Baphomet2015/Formant_V2/Doc/Formant_V2_Capitulo_05.docx

# 1 formant v2: módulos

En este capítulo se analizarán los distintos módulos que integran el Formant V2.

Para cada módulo se detallarán las modificaciones realizadas (en caso de haberlas) y se dará referencia del capítulo que recoge la información del módulo en cuestión en el documento original del formant (ElektorFormantMusicSynthesiser.pdf).

Las mejoras introducidas han dotado al Formant V2 de una mayor capacidad y versatilidad de utilización pero siempre manteniendo intacta la esencia del diseño original, esto es, la generación de un sonido puramente analógico que es la característica más importante de este sintetizador de música tan especial.

## 1.1 módulo interfaz de teclado

Documentación original ElektorFormantMusicSynthesiser.pdf: Capítulos 2 y 3

Con el fin de dotar al Formant V2 de una mayor capacidad de control y versatilidad, se ha optado por sustituir el teclado clásico original por una interfaz MIDI.

Las ventajas de esta modificación son evidentes,

- Posibilidad de utilización de un moderno teclado MIDI.
- Integración del Formant V2 en un sistema de generación de música por ordenador.

La siguiente figura ilustra el interfaz propuesto,

INTERFACE TECLADO ORIGINAL FORMANT

KOV

GATE

MIDI IN

MIDI THRU

CONTROLADOR

MIDI

KBV

GATE

C

E

B

D

Figura 1. Diagrama de la interfaz de teclado MIDI

Nota:

Los puntos B, C, D y E son las señales correspondientes en el esquema de la interfaz de teclado original del Formant.

Este hecho sin embargo plantea diversos problemas técnicos.

En el diseño original del Formant se utilizó un teclado SKA de 37 teclas (3 octavas) en el cual, cada tecla accionaba dos “pulsadores” independientes, uno era utilizado para la generación de una cierta tensión correspondiente a la tecla pulsada (señal KOV que posteriormente controlaba los VCOs y VCFs) y otro erautilizado en la generación del pulso que se utiliza para disparar los diversos módulos que intervienen en el modelado del sonido (VCAs, ADSRs).

El primer paso para poder utilizar una señal MIDI será la implementación de una interfaz “MIDI → 1V/Octava” que por un lado implemente la interfaz MIDI con el exterior y por otro permita obtener las dos señales que generaba el teclado clásico del formant, esto es, la señal KBV y la señal GATE y que posteriormente se introducirán en el circuito original e interfaz de teclado el cual a su vez proporcionará las señales KOV y GATE al resto de módulos.

Otra consideración en el diseño es que como se ha comentado, el teclado original del formant disponía de 3 octavas, pero en la actualidad es difícil encontrar teclados MIDI con tres octavas por lo que se ha optado por ampliar la capacidad total del teclado a 4 octavas.

### 1.1.1 señal kbv

El Formant es un sintetizador de tecnología “1V / Octava”, esto significa que para cada aumento de 1V en la entrada, la frecuencia de salida aumentará en una octava (es decir, en un factor de 2).

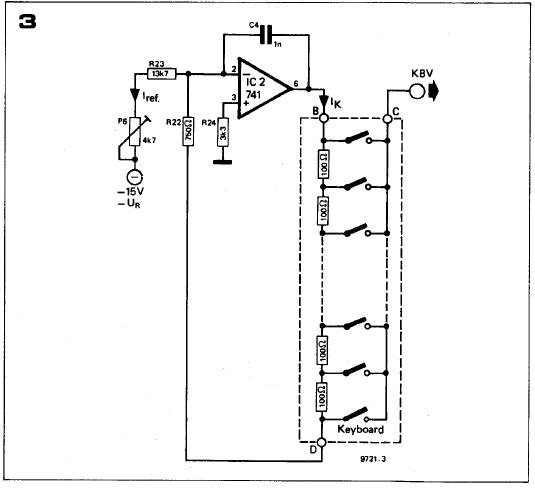
[picture p85: figure]

Cada octava tiene 12 semitonos por lo que obtenemos 1V/12 = 83,3mV por semitono, en el diseño original del Formant esta tensión se consigue mediante un divisor de tensión por el que circula una corriente constante (ver figura 3, en el capítulo 2 de la documentación original), de esta forma además se consigue que en caso de pulsar dos o más teclas simultáneamente bien accidentalmente o intencionadamente, solo se obtenga la nota de la tecla más grave, obteniendo así la característica de teclado monofónico del Formant, esta tensión es la que genera la señal KBV (Keyboard Voltage) como salida del generador 1V/Octava.

Figura 2. Generador 1V/Octava original.

Este circuito debe ser modificado de acuerdo al nuevo requerimiento de funcionamiento, el circuito resultante es el mostrado a continuación,

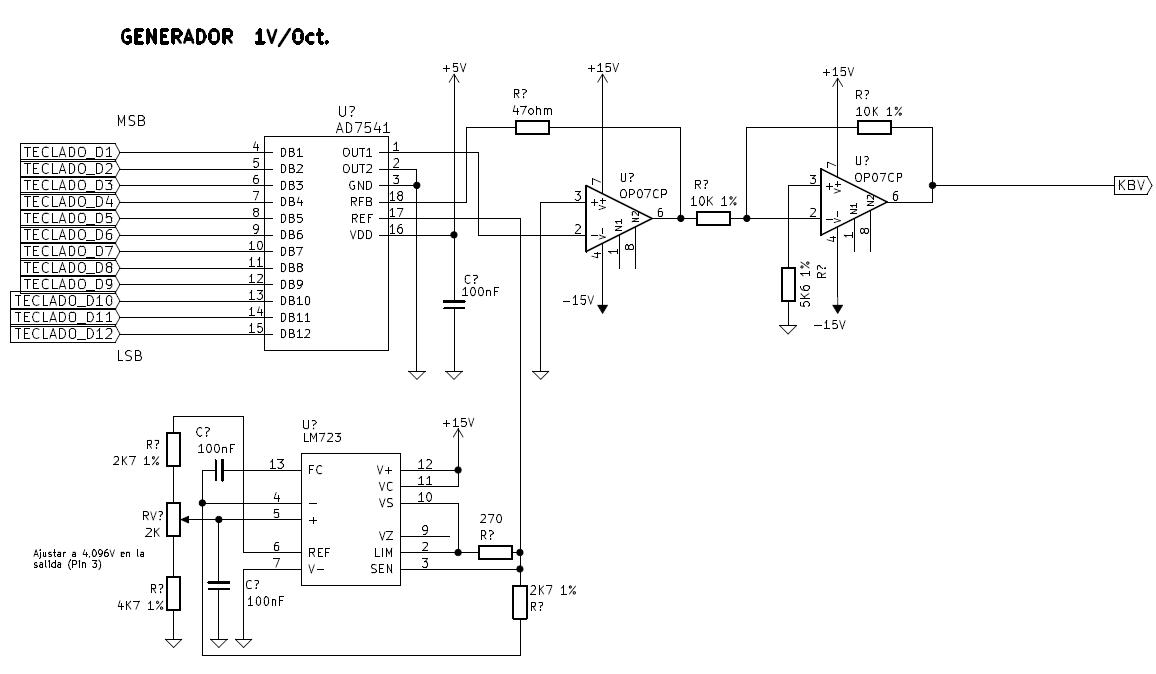
[picture p86: figure]

Figura 3. Generador 1V/Octava MIDI.

Como se puede apreciar, el circuito propuesto está implementado entorno a un conversor Digital/Analógico DAC de 12 Bits, el AD7541 de Analog Devices.

Este conversor recibe en sus entradas un cierto código y genera en su salida una tensión equivalente.

La tensión de referencia de este conversor se obtiene de un regulador muy preciso y estable implementado con un circuito LM723 (el mismo que se utiliza en la fuente de alimentación para obtener las tensiones generales de +15V, -15V y +5V). Este regulador estará ajustado para que su salida genere una tensión de 4,096 voltios, que utilizada como tensión de referencia para el DAC permitirá obtener tensiones en múltiplos de 1mV.

#### 1.1.1.1 Ajuste de la tensión de referencia

Se deberá ajustar la tensión de salida del LM723 medida en la entrada REF (pin 17) del AD7541, para obtener una tensión de 4,096V.

Dado que el conversor D/A posee 12Bits de resolución, esto permitirá obtener 4096 pasos, lo cual unido a la utilización de una tensión de referencia de 4,096V permite obtener tensiones de 1mV lo que finalmente conllevará en la obtención de las tensiones en incrementos de 83mV necesarios para implementar la característica 1V/Octava.

El hecho de utilizar un conversor D/A de 12Bits, unido a la tensión de referencia de 4,096V permite además abarcar el rango de 4 octavas propuesto.

El controlador MIDI cargará en el registro de salida formado por los dos C.I. 74HC593 el código equivalente a la tecla pulsada, este código es el que a su vez sirve de entrada para el código de entrada en el DAC.

### 1.1.2 señal gate

La segunda señal que se debe obtener del teclado es la denominada GATE, esto es un pulso de tensión que se genera cuando se pulsa alguna tecla en el teclado y que es utilizado como señal de disparo de diversos módulos del Formant (ADSR, VCAs, VCFs etc).

Esta señal que en el Formant original era generada por el segundo pulsador asociado a cada tecla y que se obtenía en los puntos A y E del teclado será generada directamente desde el circuito de interfaz MIDI e introducida finalmente en el punto E (GATE) del circuito de interfaz de teclado original.

### 1.1.3 señal kov

La señal KOV (Keyboard Output Voltage) es la señal más importante del Formant ya que comanda prácticamente todos los módulos del sintetizador.

Se genera a partir de la señal KBV, obtenida desde el circuito que realiza la interfaz MIDI y posterior característica 1V/Octava y es la resultante de “sumar” a esta señal KBV las tensiones aportadas por los potenciometros COARSE, FINE, PORTAMENTO y FM provinientes de la interfaz de teclado.

El circuito KOV propuesto se muestra en la siguiente figura,

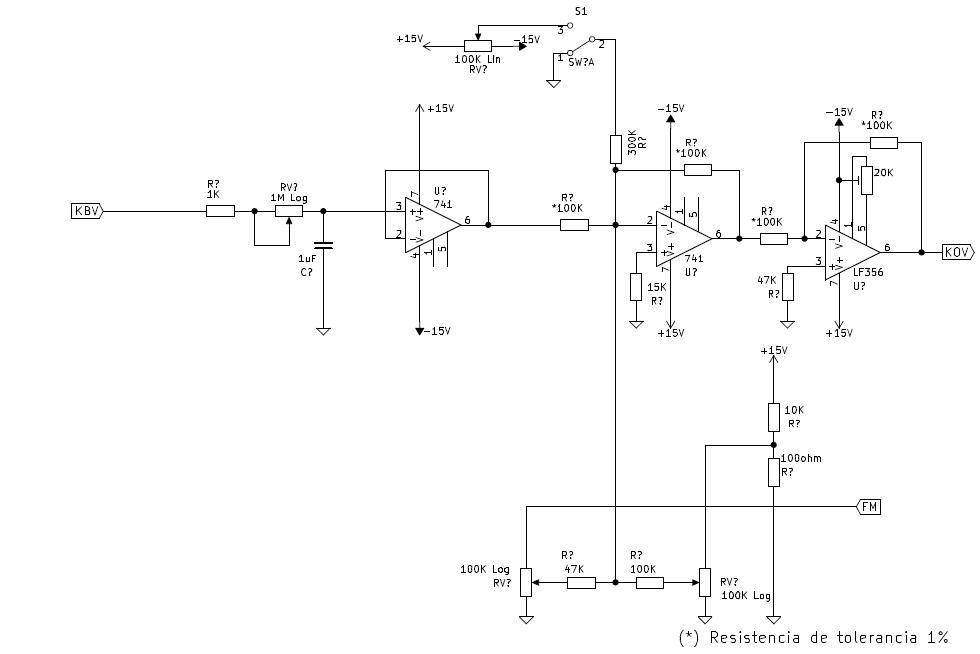
[picture p87: figure]

Figura 4. Circuito KOV.

La nueva versión difiere en gran medida de la original del Formant ya que, entre otras cosas elimina la etapa “Sample & Hold” del diseño original, efectivamente en el diseño original la señal KBV se inyectaba a una etapa de Sample & Hold con el fin de mantener la tensión de la tecla pulsada cuando el usuario deja de pulsar dicha tecla, esto es necesario para poder efectuar algunos efectos tales como el “portamento”. Debido al diseño original, cuando el usuario dejaba de pulsar una tecla la tensión generada por dicha tecla desaparecía inmediatamente lo que hacía imposible obtener el efecto de portamento, para ello se incluyó un circuito de Sample & Hold, el cual “muestreaba y retenía” la tensión de la tecla aún después de que dicha tensión desapareciera al dejar de pulsar la tecla, en el nuevo diseño esta etapa de retención es innecesaria ahora ya que el controlador MIDI cuando recibe el comando de tecla pulsada calcula el código correspondiente a dicha tecla y lo carga en el registro formado por los dos circuitos HC595 que alimentan la entrada del conversor D/A sustituyendo el código que previamente exista, posteriormente cuando el usuario deja de pulsar la tecla, el código de dicha tecla permanecerá en el registro dado que el controlador MIDI NO lo elimina, esto hace que la salida del D/A mantenga la tensión de dicha tecla aún después de que el usuario haya dejado de pulsar la tecla correspondiente, haciendo innecesaria la operación de retención o Sample & Hold.

La señal KBV se inyecta directamente al potenciometro de 1M que junto con el condensador de 1uF y el operacional en modo seguidor de tensión permiten obtener el efecto de portamento, tal y como se hacía en el diseño original.

Finalmente la señal KBV acondicionada se suma al circuito sumador de las tensiones de COARSE, FINE y FM, en esta parte el diseño original aportaba una compensación de offset para poder ajustar dicho offset final que en el nuevo diseño se elimina, sustituyendolo por el offset del amplificador operacional final.

#### 1.1.3.1 Ajuste del offset final.

Para ajustar el offset final se deberá inicializar el interfaz MIDI, esto se consigue al dar alimentación (power ON) o bien pulsando el pulsador de RESET general del Formant.

Después de inicializar el interfaz NO se debe pulsar ninguna tecla en el teclado, dado que inmediatamente después de la inicialización del interfaz, el código cargado en el D/A es 0 por lo que la señal KBV es 0 voltios.

Con un multímetro en la escala de voltios (o milivoltios si está disponible) se deberá ajustar el valor de la tensión KOV a 0 voltios, idealmente la tensión de la señal KOV deberá medirse en el circuito “receptor” de las señales GATE y KOV con el fin de incluir en la medida las posibles pérdidas de tensión que se pudieran producir en el cable que lleva la señal KOV hasta la etapa receptora de estas señales.

### 1.1.4 etapa receptora de las señales kov y gate

El diseño original del Formant incorpora una etapa receptora de las señales KOV y GATE, la cual recibe dichas señales desde el circuito generador y “compensa” las posibles pérdidas en dichas señales debidas por ejemplo a la longitud de los cables que las conectan.

Esta etapa permanece sin cambios respecto al diseño original, (ver figura 5, en el capítulo 3 de la documentación original).

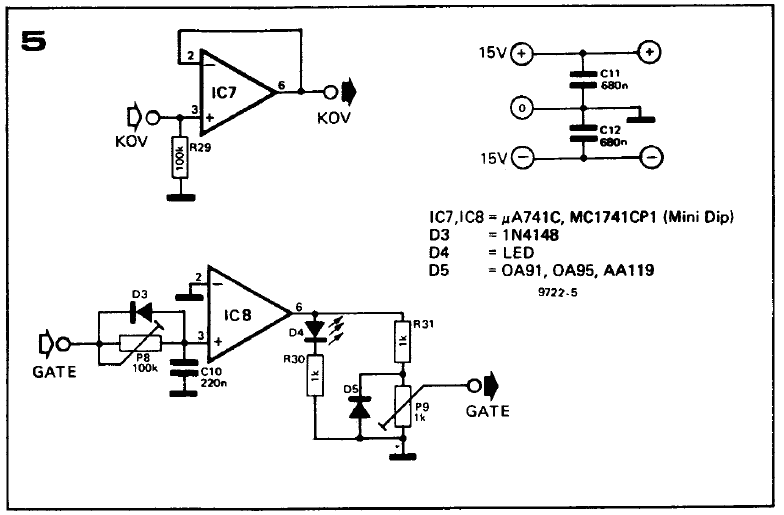
[picture p88: figure]

### 1.1.5 interfaz midi

La interfaz MIDI esta implementada utilizando un microcontrolador de tecnología openSource de Arduino, concretamente el modelo Arduino Nano.

Este microcontrolador recibe la señal MIDI-IN, decodifica los mensajes que se pueden utilizar para el control del Formant V2 y genera las señales correspondientes.

El canal MIDI que se asigna al Formant deberá ser fijado con los microinterruptores de configuración dispuestos a tal efecto.

Finalmente existe un pulsador de TEST para tareas de depuración y comprobación de funcionamiento, para activar el modo test se deberá seguir la siguiente operativa:

- Conectar el microcontrolador (utilizando el conector USB el mismo) con un ordenador (PC, portátil etc).

Atención:

Dependiendo de la versión de sistema operativo, es posible que sea necesario instalar determinados drivers, en este caso visitar el sitio web oficial de Arduino,

https://www.arduino.cc/en/Guide/Windows#

- Mantener pulsado el pulsador de TEST mientras se conecta el Formant V2 (power ON), al hacerlo y tras el arranque del microcontrolador, el Led de “señal MIDI” parpadeará indicando que se ha entrado en el modo test.
- Utilizar un programa de tipo Monitor Serie convencional para poder recibir la información enviada por el microcontrolador, seleccionando el puerto serie que ha montado el cable utilizado, normalmente estos puertos serie se reconocen porque si identifican con un valor COM distinto de COM1 o COM2 (puede ser COM3, COM4 o mayor).

Importante:

Se debe seleccionar una velocidad de transmisión en el programa monitor de 31250 Bps debido a que es la velocidad de operación del interfaz MIDI.

No todos los terminales serie permiten seleccionar esta velocidad por lo que dicho programa deberá tener la posibilidad de elegir esta velocidad.

Una vez establecida la comunicación entre el interfaz MIDI y el ordenador, se deberá recibir en el programa terminal un texto similar a este,

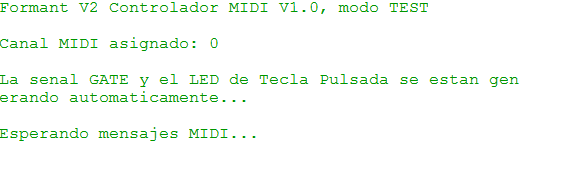
[picture p89: figure]

Ahora, si se reciben mensajes MIDI, estos NO se ejecutarán sino que la información relativa a los mismos será decodificada y enviada al programa terminal, como por ejemplo,

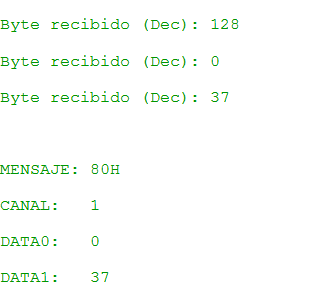
[picture p90: figure]

La interfaz MIDI del Formant V2 no solo permite controlar el teclado, respondiendo a los mensajes Note ON y Note OFF sino que también soporta las siguientes funciones:

- Control de volumen general del canal.

Mensaje MIDI Control Change (cambio de control), Control Change 7: Volumen

Este mensaje MIDI permite ajustar el volumen general de salida del Formant V2, que está situado en el Módulo COM, consultar el apartado 2.2 para más información.

Por último, las señales KBV y GATE generadas desde la interfaz MIDI alimentarán el circuito de interfaz de teclado original del formant que está recogido en el capítulo 2, figura 10 y que se muestra a continuación,

El esquema eléctrico completo de la nueva interfaz se muestra en “Modulos->INTERFACE-TECLADO->Hw->Ver_DAC_12Bits->Formant_V2_Teclado.pdf”

## 1.2 módulo fuente de alimentación

Documentación original ElektorFormantMusicSynthesiser.pdf: Capítulo 3

La fuente de alimentación del formant no ha sufrido ningún cambio respecto del diseño original.

Se trata de una fuente de alimentación con tres salidas +5V, +15V y -15V muy estables y precisas siendo el diseño perfectamente válido para la nueva versión.

## 1.3 Modulo vco

Documentación original ElektorFormantMusicSynthesiser.pdf: Capítulos 4 y 5

## 1.4 modulo vcf

Documentación original ElektorFormantMusicSynthesiser.pdf: Capítulo 6

## 1.5 modulo vcf 24dB

Documentación original ElektorFormantMusicSynthesiser.pdf: Capítulo 7

## 1.6 modulo rfm

Documentación original ElektorFormantMusicSynthesiser.pdf: Capítulo 8

## 1.7 adsr

Documentación original ElektorFormantMusicSynthesiser.pdf: Capítulo 9

El formant incorpora módulos ADSR para la generación de envolventes destinados a modular las señales suministradas desde los VCFs y también para el control del VCA.

En una implementación “clásica” del formant se necesitarían al menos dos módulos ADSR con el fin de lograr la mayor versatilidad posible, uno se destinaría a modular las señales de los VCOs y VCFs y otro para el control del módulo VCA.

En el Formant V2 se propone la implementación de un ADSR DUAL, es decir de un único circuito que soportará dos módulos ADSR totalmente independientes con características idénticas a los ADSR originales del formant.

Para el diseño de este módulo ADSR se utilizará tecnología basada en microprocesador, de igual manera que se ha utilizado para la nueva interfaz de teclado.

Es importante destacar que la versión dual propuesta no incluye ninguna “ventaja” significativa con respecto al circuito ADSR original sino que es más bien una actualización del diseño original adaptándolo a las nuevas tecnologías basadas en microprocesador y si hubiera que destacar alguna ventaja de esta actualización del diseño con respecto al original podríamos hacer hincapié en una reducción de tamaño del circuito y mayor precisión en los tiempos de control pero realmente estas mejoras no afectan significativamente al rendimiento general del circuito por lo que en suma se puede optar por la versión original, construyendo dos módulos ADSR o por esta nueva versión que incluye estos dos módulos en una sola placa de circuito, en ambos casos el resultado será el mismo.

Hecha esta puntualización y centrándonos en el nuevo diseño, indicar que el modelo de microprocesador elegido para el diseño de este módulo es el Arduino Nano (el mismo que el utilizado en la nueva interfaz de teclado) y sustituirá la parte de “control” que en el circuito original del formant generaba los diversos tramos de la envolvente (ATTACK, DECAY, SUSTAIN y RELEASE), dejando la parte de generación de las tensiones que implementan los tramos de la envolvente exactamente como estaba en el diseño original.

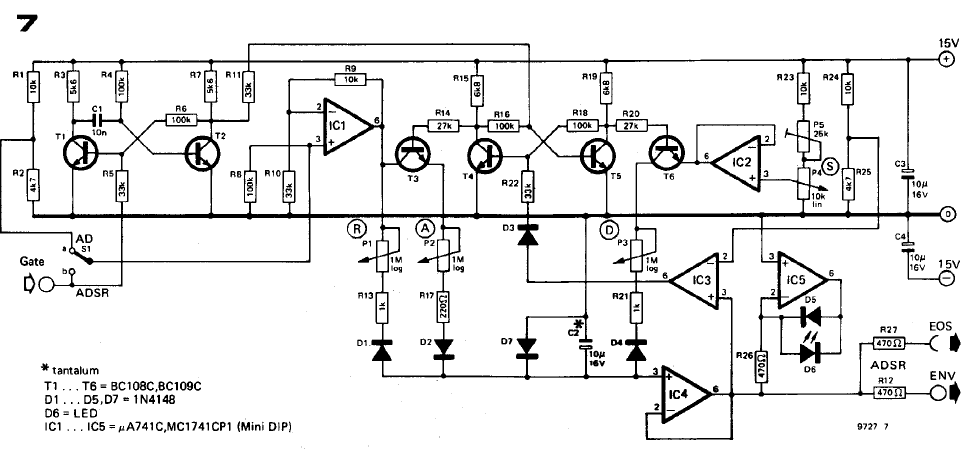
[picture p91: figure]

Figura 5. Módulo ADSR original del Formant

Capítulo 9 en documentación original del formant.

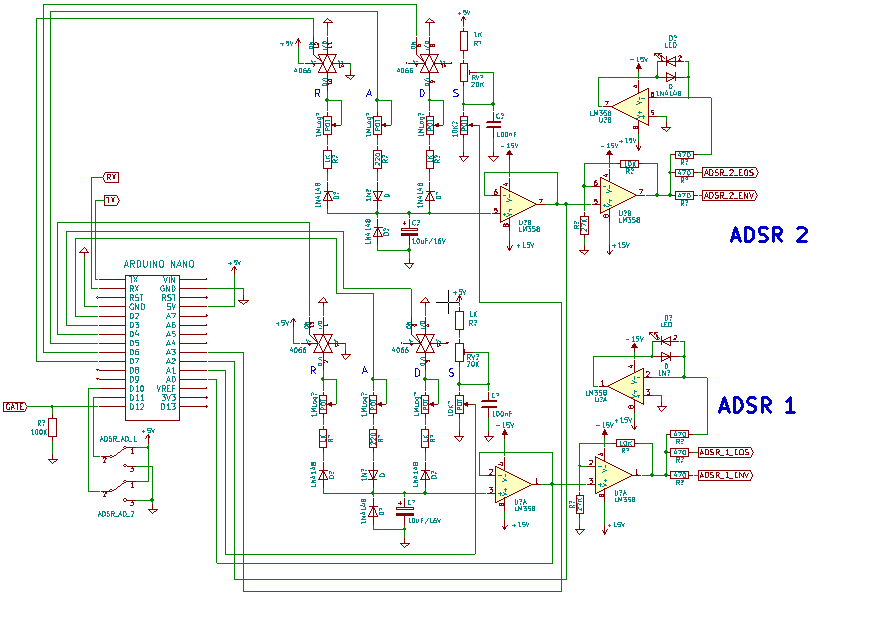
[picture p92: figure]

Figura 6. Módulo ADSR en Formant V2.

Disponible en la carpeta Modulos->ADSR del proyecto.

## 1.8 modulo vca

Documentación original ElektorFormantMusicSynthesiser.pdf: Capítulo 10

## 1.9 módulo lfoS

Documentación original ElektorFormantMusicSynthesiser.pdf: Capítulo 11

## 1.10 módulo noise

Documentación original ElektorFormantMusicSynthesiser.pdf: Capítulo 11

## 1.11 módulo com

Documentación original ElektorFormantMusicSynthesiser.pdf: Capítulo 12

El módulo denominado COM (Control and Output Module) representa la “etapa” final de salida del formant, implementando una salida directa y otra a través de un control de tono con ajuste bass, middle, trebble y volumen, con una salida final amplificada para cascos.

Este módulo también permite monitorizar el estado de las tensiones de alimentación, así como las señales de gate y xx.

El módulo COM tiene un ajuste de volumen, que se realiza mediante dos potenciomentros que permiten ajustar el volumen de la salida general.

Con el fin de poer ajustar este volumen tanto de forma manual (caso del módulo COM original) como vía MIDI se ha realizado la siguiente modificación en el circuito,

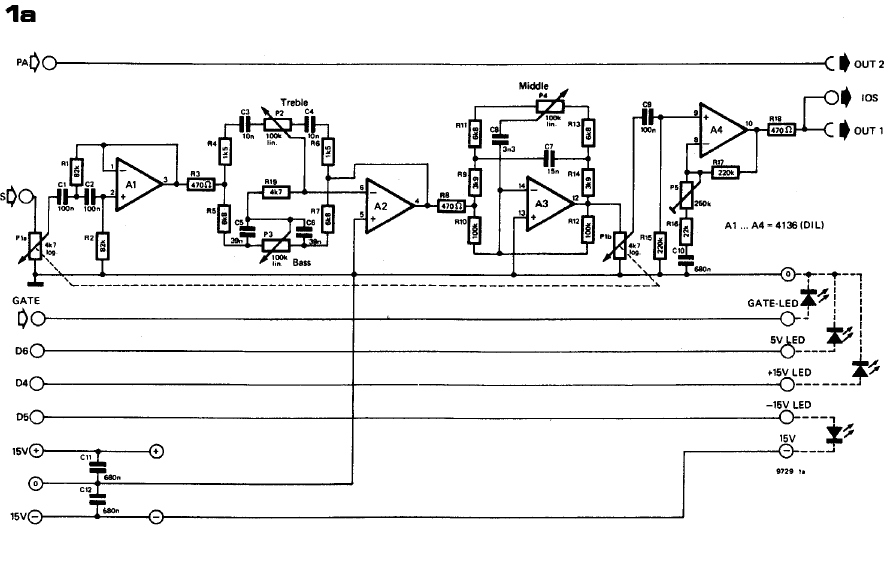
[picture p93: figure]

Figura 7. Módulo COM original del Formant.

Capítulo 12 en documentación original del formant.

Figura 8. Módulo COM en Formant V2.
