Baphomet2015/Formant_V2/Doc/Notas_Potenciometros.txt

Identificacion del tipo de potenciometros
Junto al valor puede aparecer algo como esto:

- Lin Son LINEALES
- Log Son Logaritmicos
- A   Significa Audio (logaritmicos) 
- B   Son lineales
