Baphomet2015/Formant_V2/Doc/Frecuencia de las notas musicales en hertzios.jpg

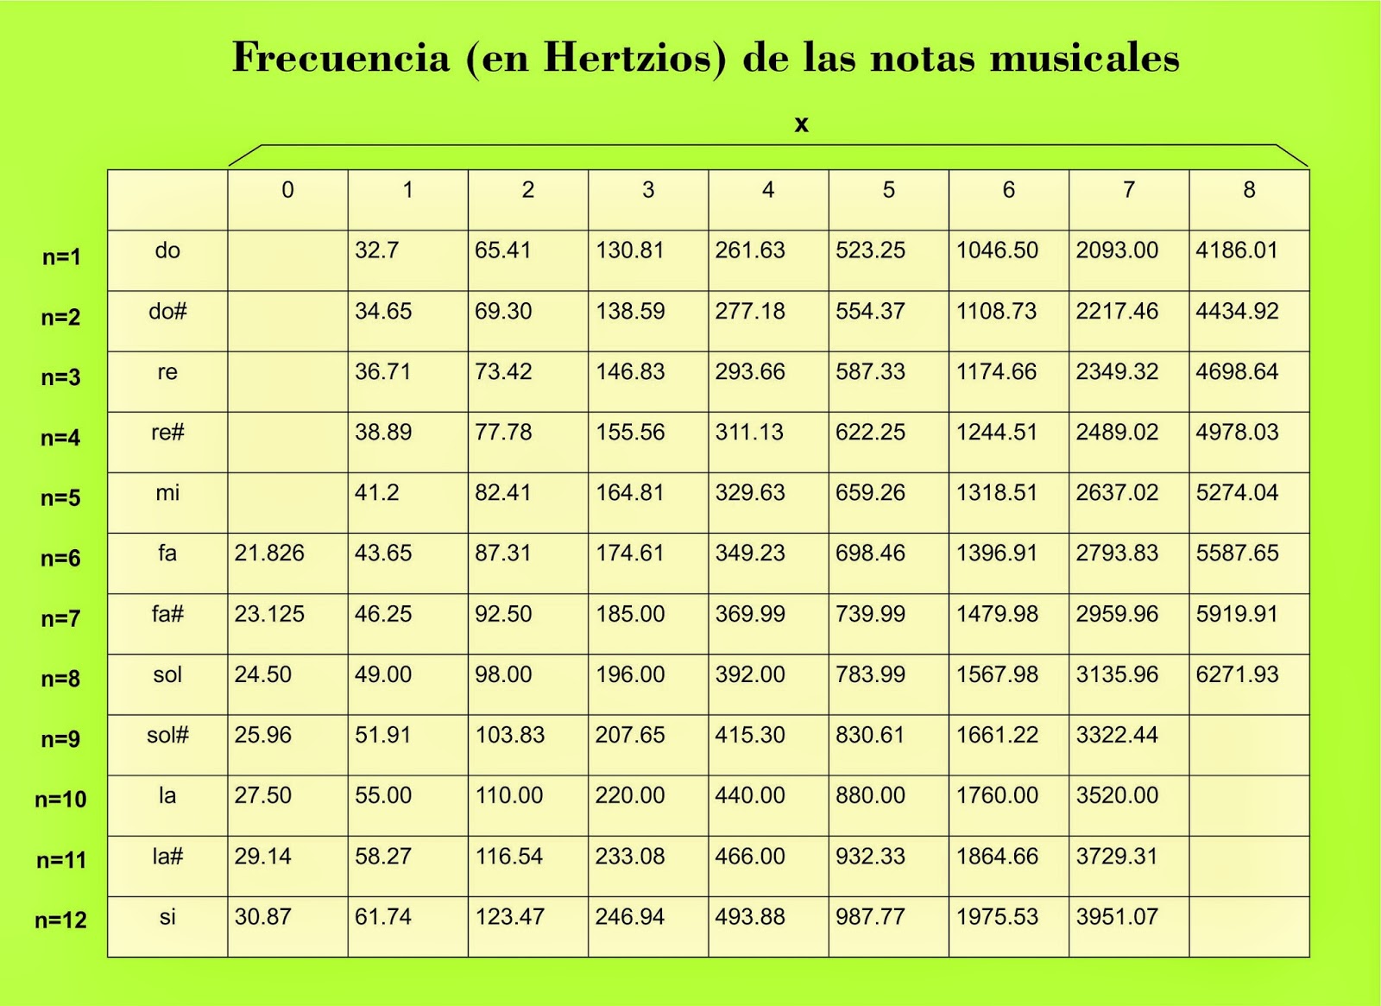
Doc/Frecuencia de las notas musicales en hertzios.jpg
