Baphomet2015/Formant_V2/Doc/Teclado_MIDI_Fig_6.jpg

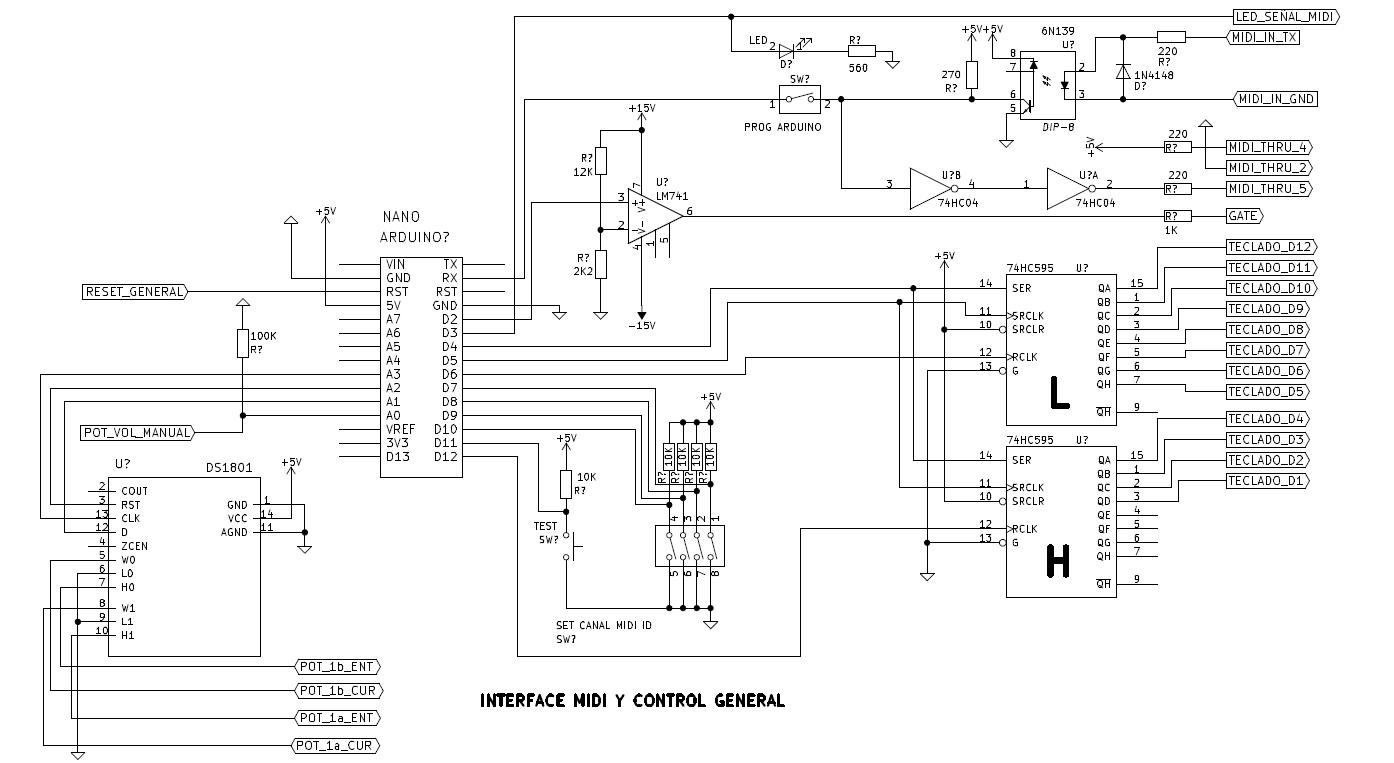
Doc/Teclado_MIDI_Fig_6.jpg
