Baphomet2015/Formant_V2/Modulos/ADSR/Fotos/P_20171114_211551.jpg

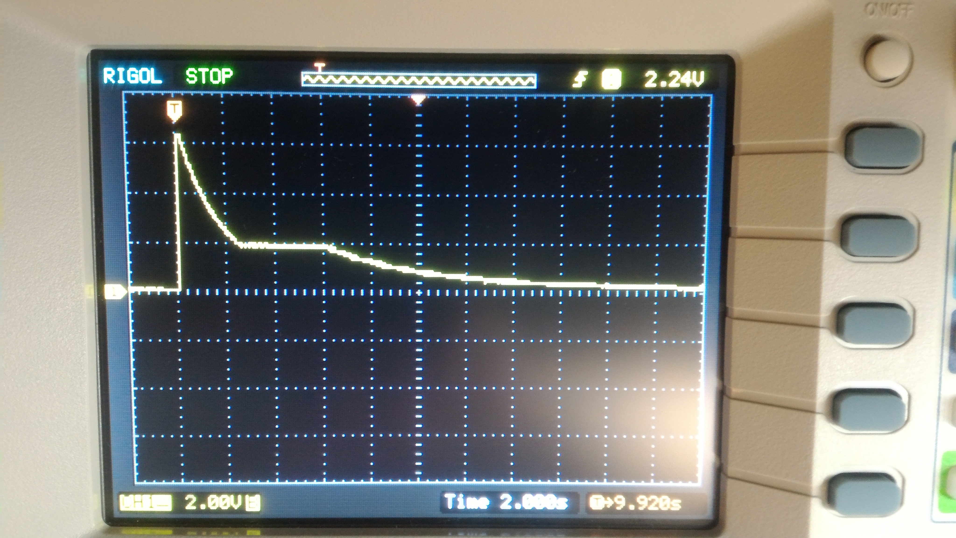
Modulos/ADSR/Fotos/P_20171114_211551.jpg
