Baphomet2015/Formant_V2/Modulos/ADSR/Fotos/P_20171114_212636.jpg

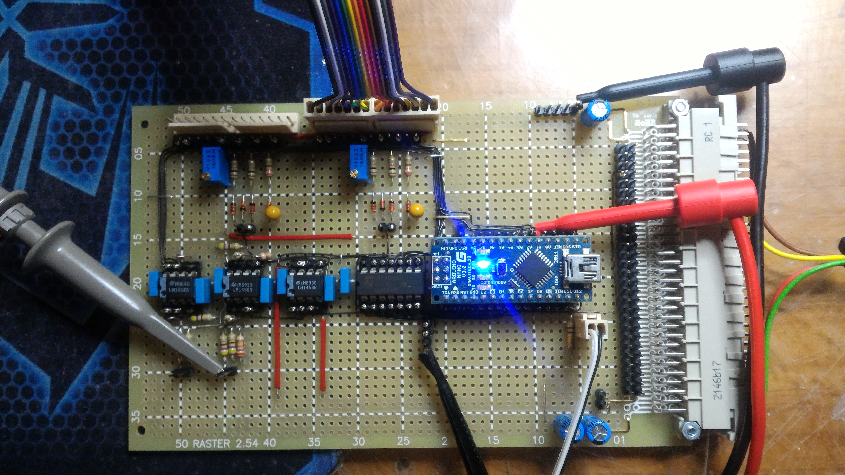
Modulos/ADSR/Fotos/P_20171114_212636.jpg
