Baphomet2015/Formant_V2/Modulos/GENERADOR_ECO/reverberator-tda10221.gif

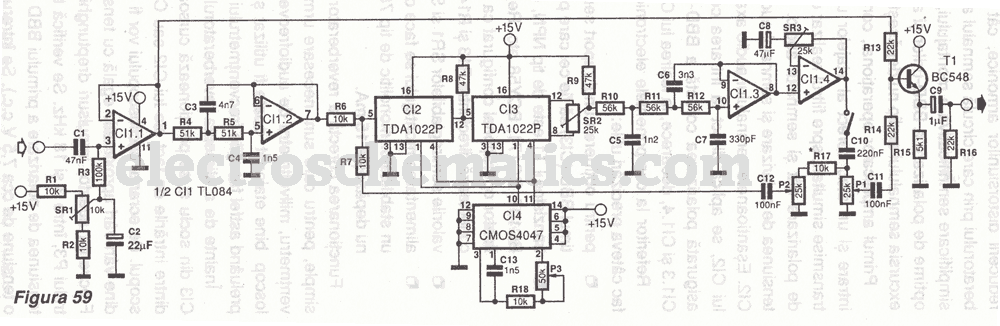
Modulos/GENERADOR_ECO/reverberator-tda10221.gif
