Baphomet2015/Formant_V2/Modulos/RITMOS/CORON_DS7/ds7sh.gif

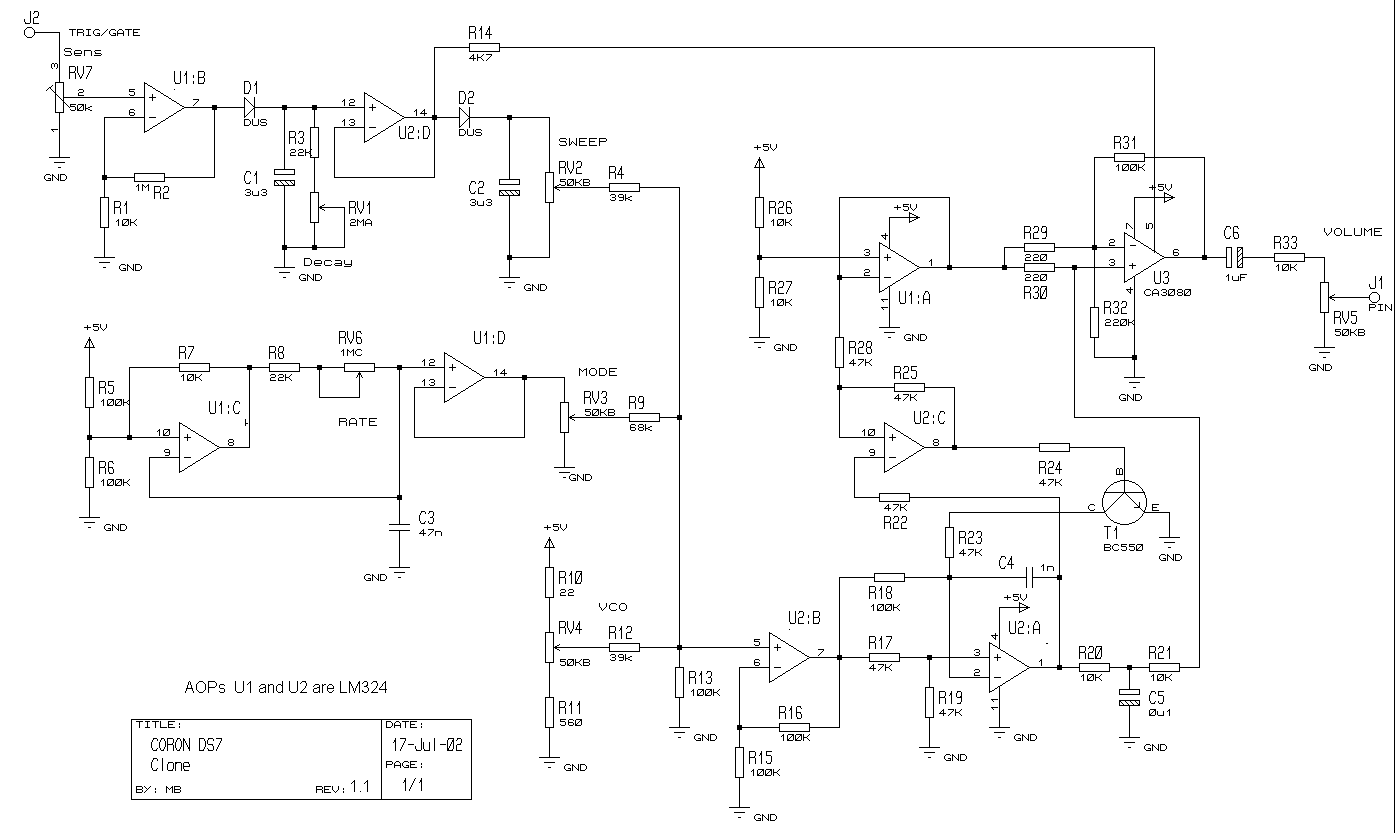
Modulos/RITMOS/CORON_DS7/ds7sh.gif
