Baphomet2015/Formant_V2/Modulos/RITMOS/Roland TR-909/ht.gif

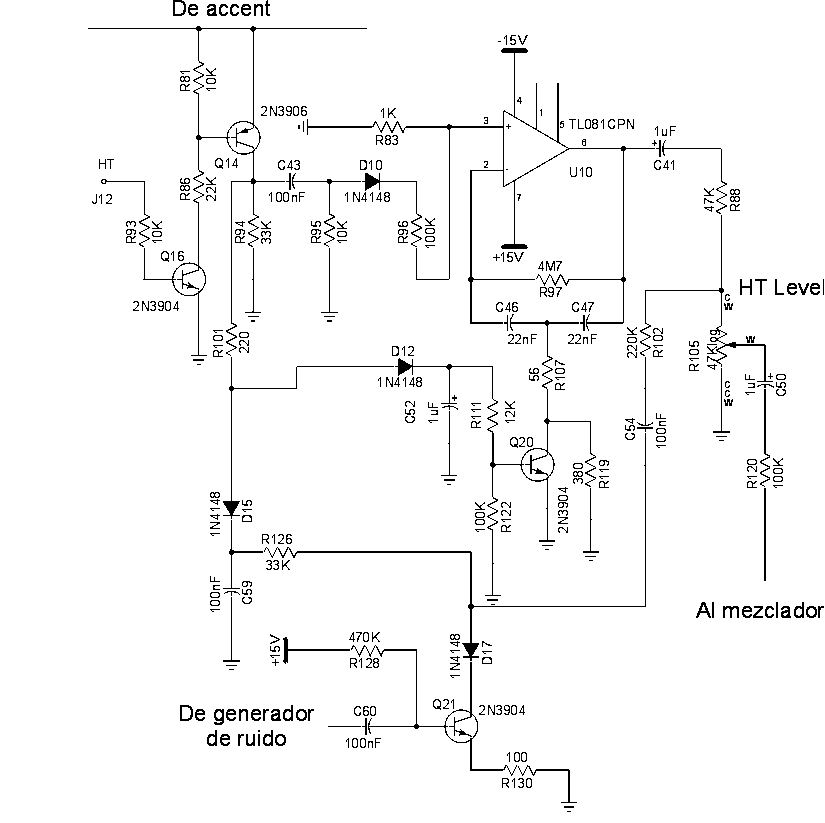
Modulos/RITMOS/Roland TR-909/ht.gif
