Baphomet2015/Formant_V2/Modulos/RITMOS/Roland TR-909/noise.gif

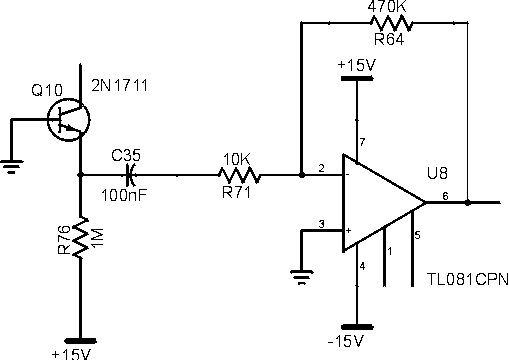
Modulos/RITMOS/Roland TR-909/noise.gif
