Baphomet2015/Formant_V2/Modulos/RITMOS/Roland TR-909/snare.gif

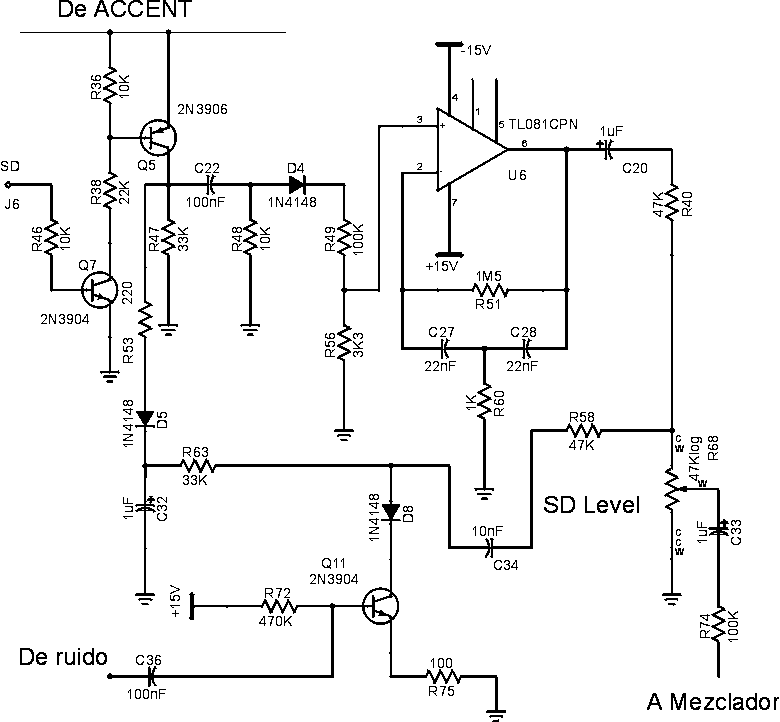
Modulos/RITMOS/Roland TR-909/snare.gif
