Baphomet2015/Formant_V2/Modulos/VCO/Fotos/P_20170926_150340.jpg

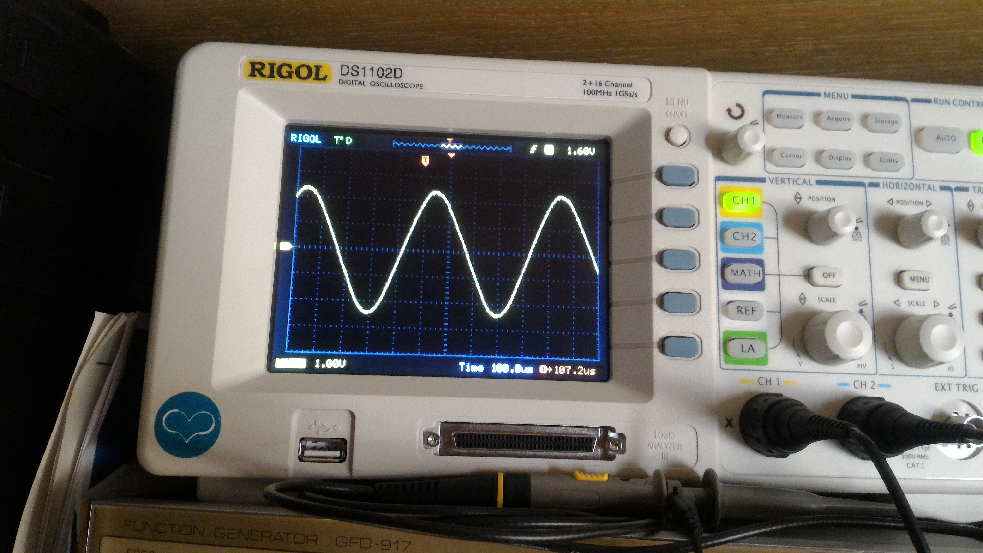
Modulos/VCO/Fotos/P_20170926_150340.jpg
