Baphomet2015/Formant_V2/Modulos/VCO/Fotos/P_20170926_150354.jpg

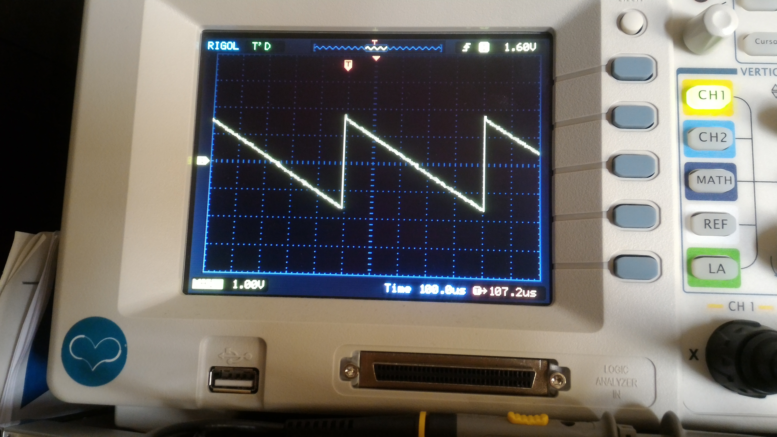
Modulos/VCO/Fotos/P_20170926_150354.jpg
