Baphomet2015/Formant_V2/Modulos/VCO/Fotos/P_20170926_150425.jpg

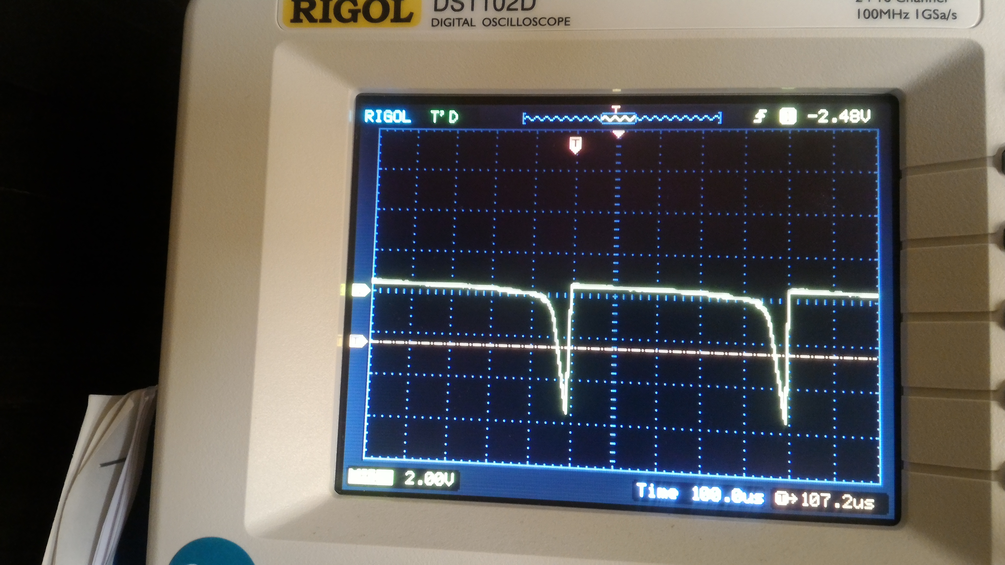
Modulos/VCO/Fotos/P_20170926_150425.jpg
