Baphomet2015/Formant_V2/Modulos/VCO/Fotos/P_20171125_213656.jpg

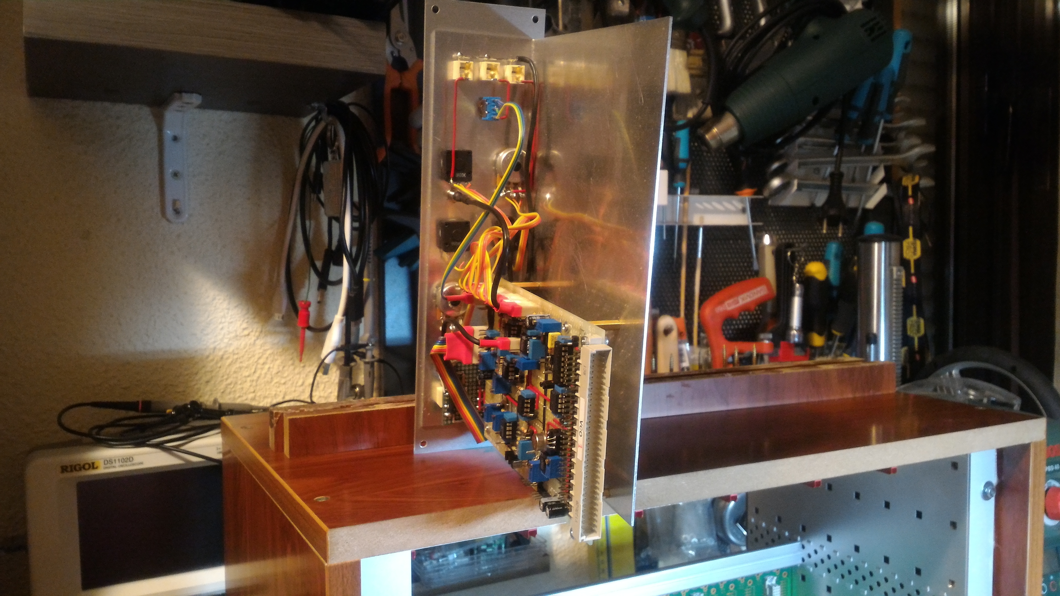
Modulos/VCO/Fotos/P_20171125_213656.jpg
