Baphomet2015/Formant_V2/Componentes_Mecanicos/Caratulas/ADSR/Caratula_ADSR.pdf

133mm (3U) | Material: | Aluminio
| Grosor: | 1mm

3,5mm Ø
X4

71 mm

6,5mm Ø
X3

10mm Ø
X4

60,50mm

121,50mm

# ADSR

ELEKTOR | FORMANT V2
FAST A SLOW | FAST D SLOW
FAST S SLOW | FAST R SLOW

ENV
INDICATOR | OUT

ADSR

AD
