Baphomet2015/Formant_V2/Componentes_Mecanicos/Caratulas/COM/Caratula_COM.pdf

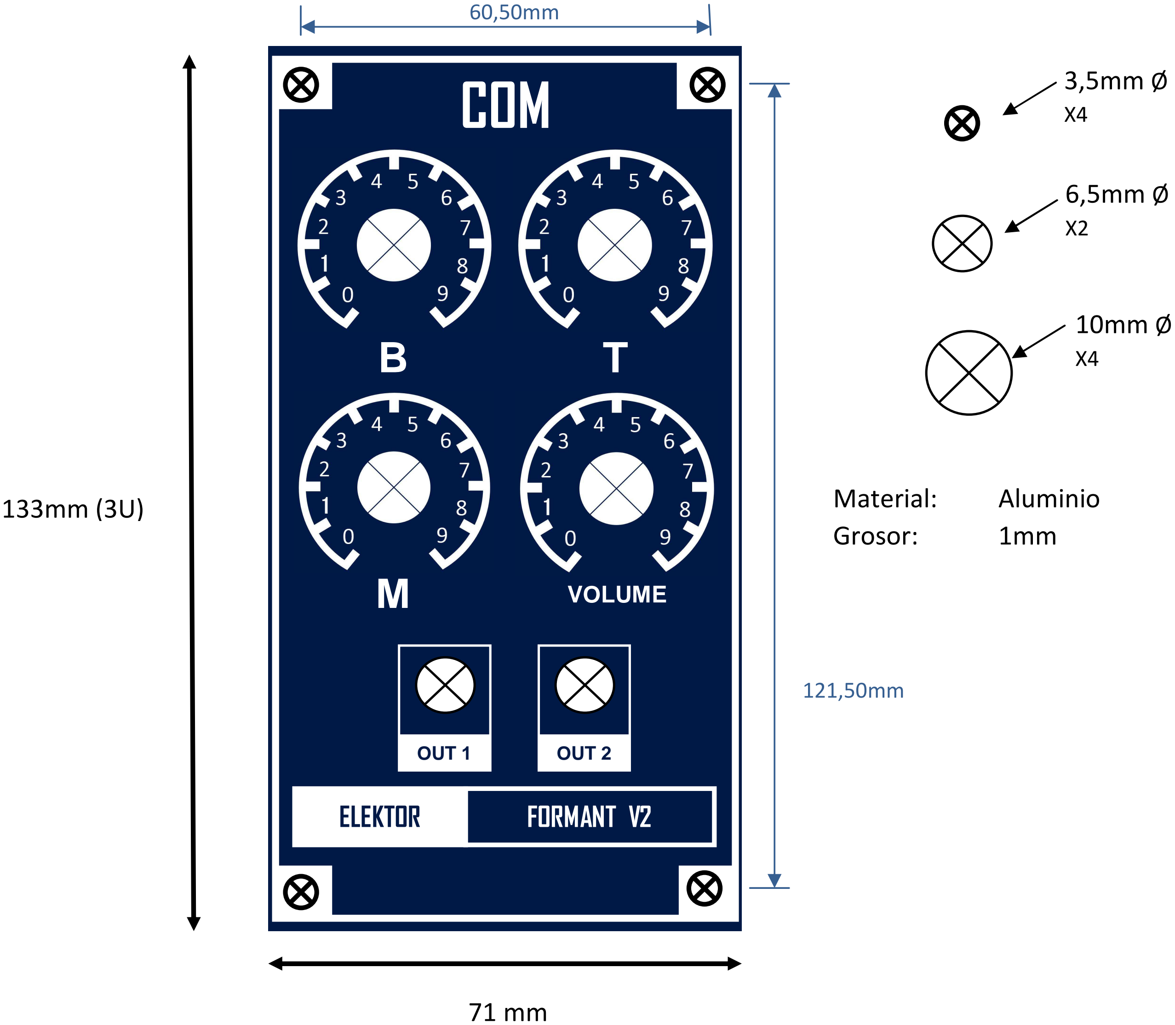
[picture p153: figure]
Material:; Aluminio; Grosor:; COM; M VOLUME; ELEKTOR; FORMANT V2; OUT 1; OUT 2
