Baphomet2015/Formant_V2/Componentes_Mecanicos/Caratulas/NOISE/Caratula_NOISE.pdf

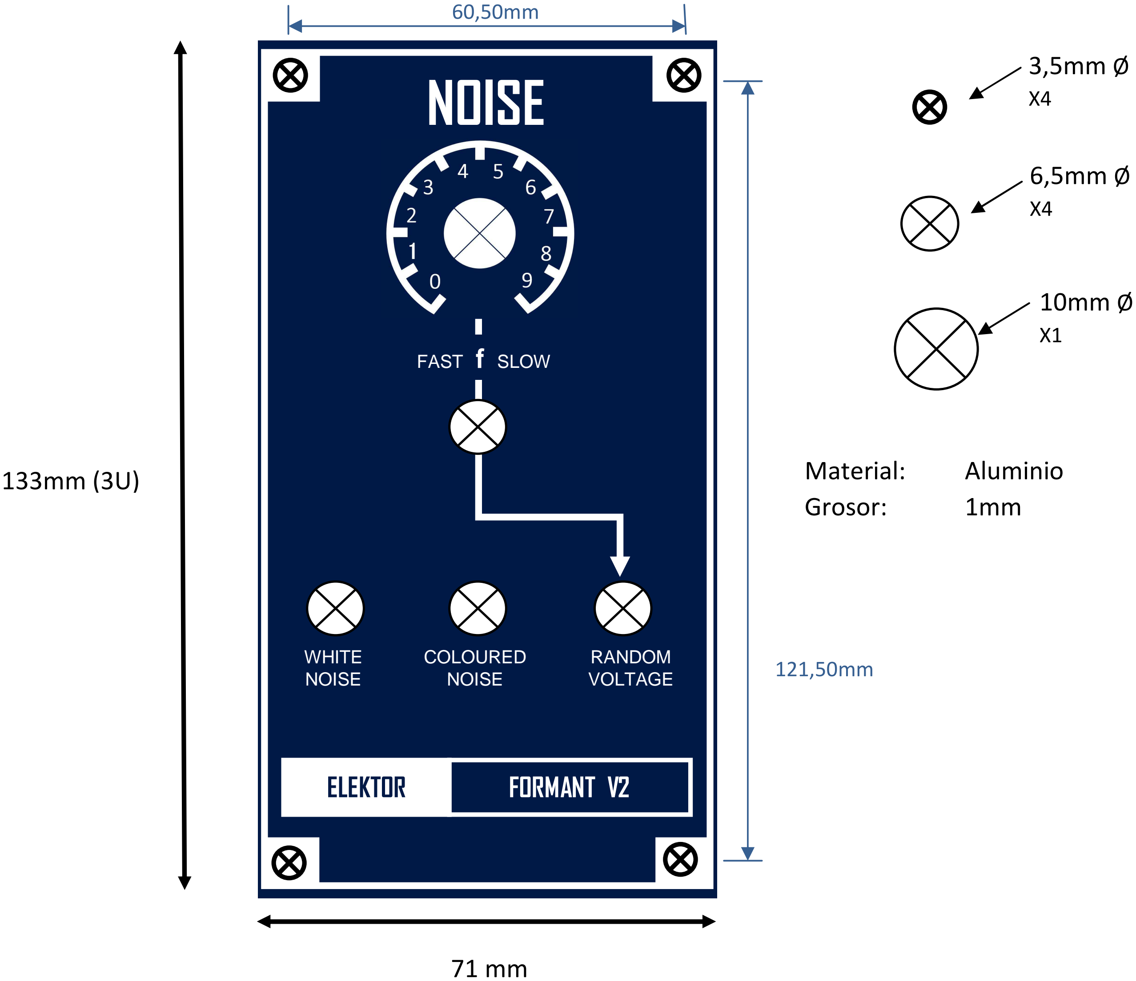
[picture p154: figure]
Material:; Aluminio; Grosor:; ELEKTOR; FORMANT V2; WHITE NOISE; COLOURED NOISE; RANDOM VOLTAGE; FAST f SLOW; NOISE
