Baphomet2015/Formant_V2/Componentes_Electronicos/Formant_V2_Reemplazados/Reemplazo_CA3084/CA3084.pdf

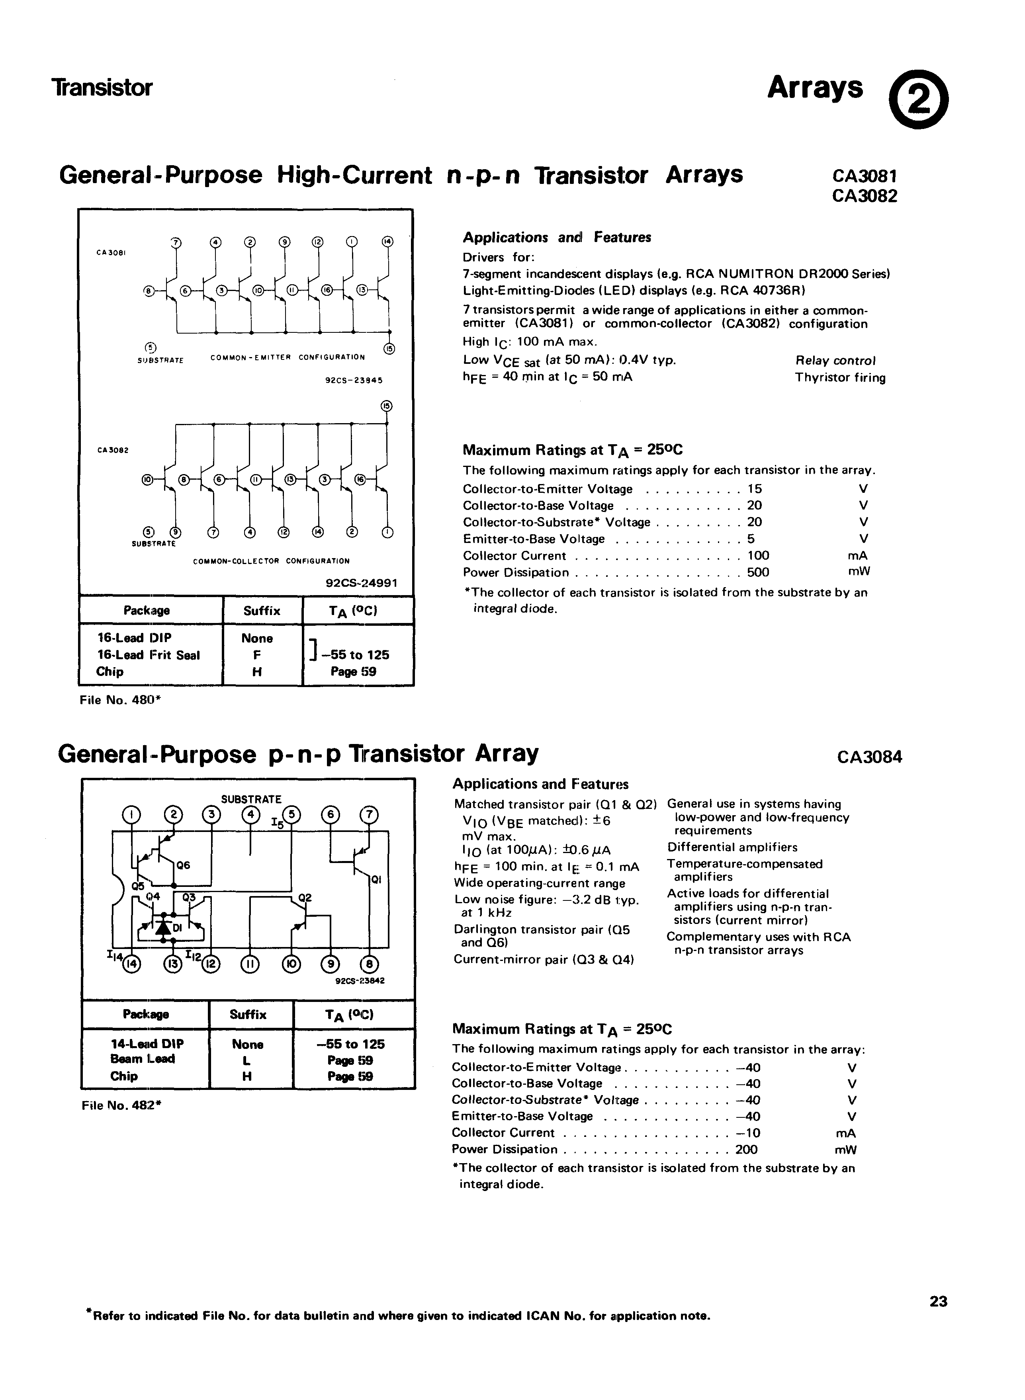
[picture p155: page 1]
