Baphomet2015/Formant_V2/Componentes_Electronicos/Formant_V2_Reemplazados/Reemplazo_UA726/UA726.pdf

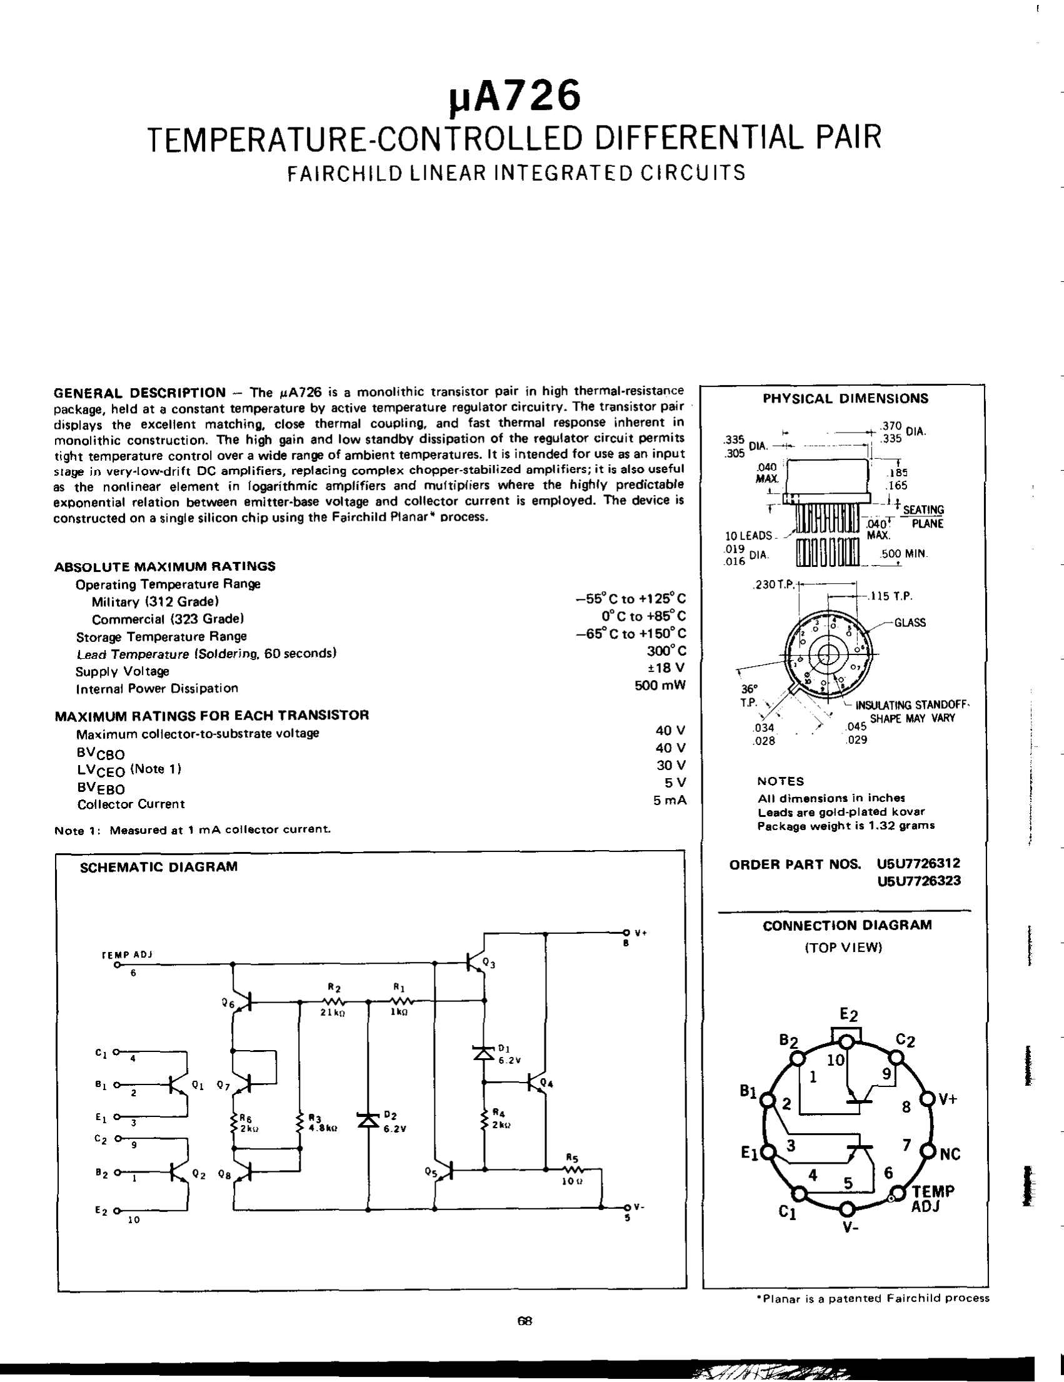
[picture p156: page 1]
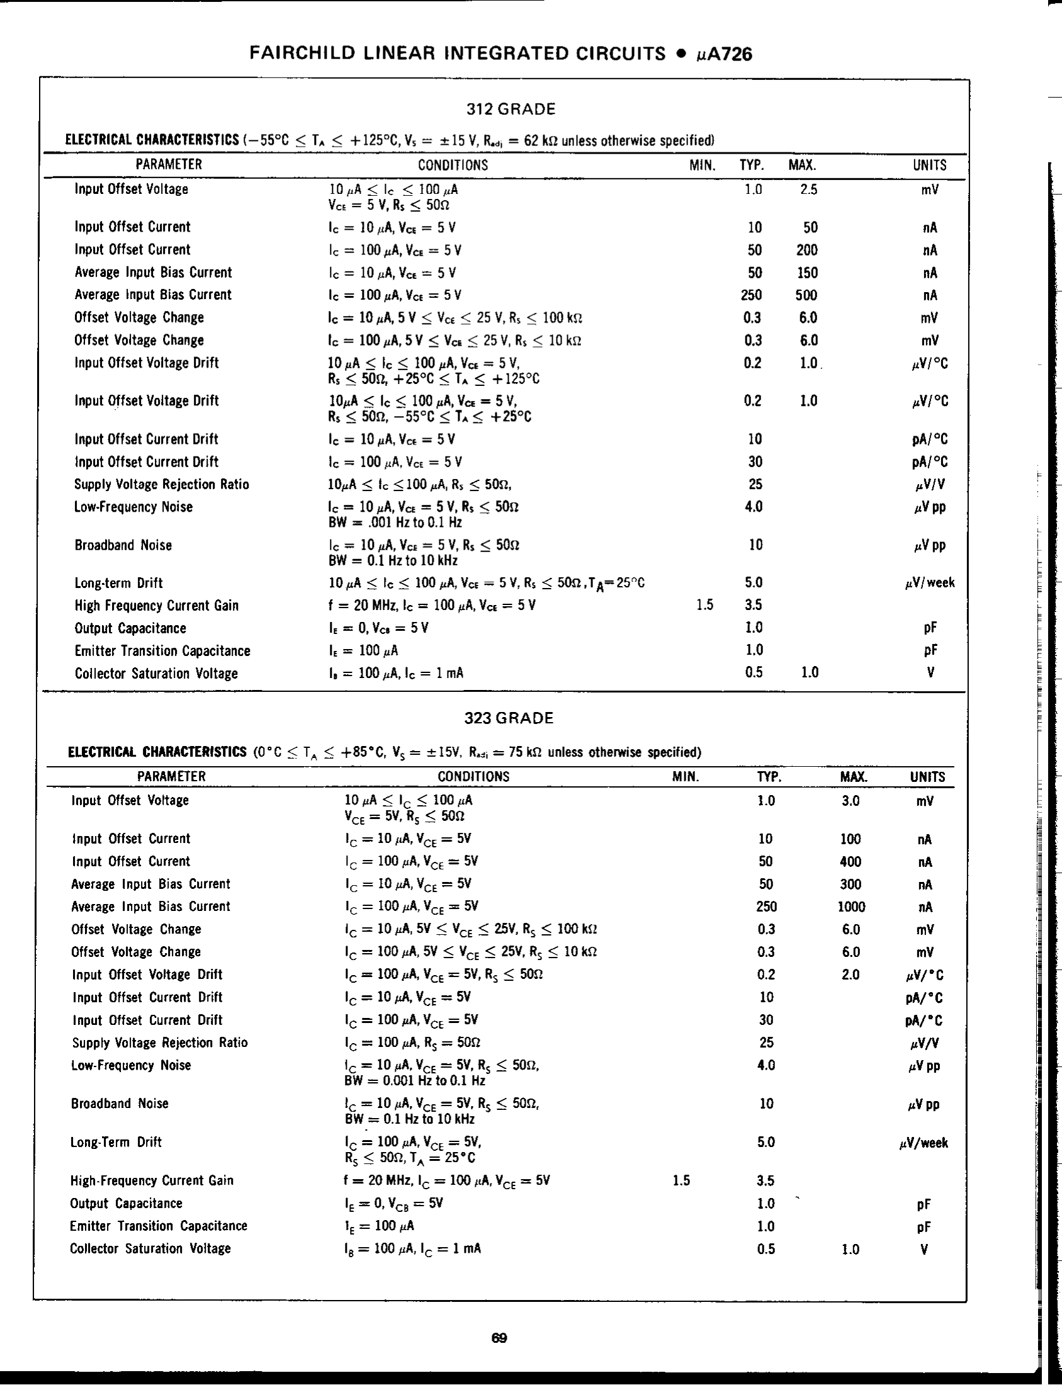
[picture p157: page 2]
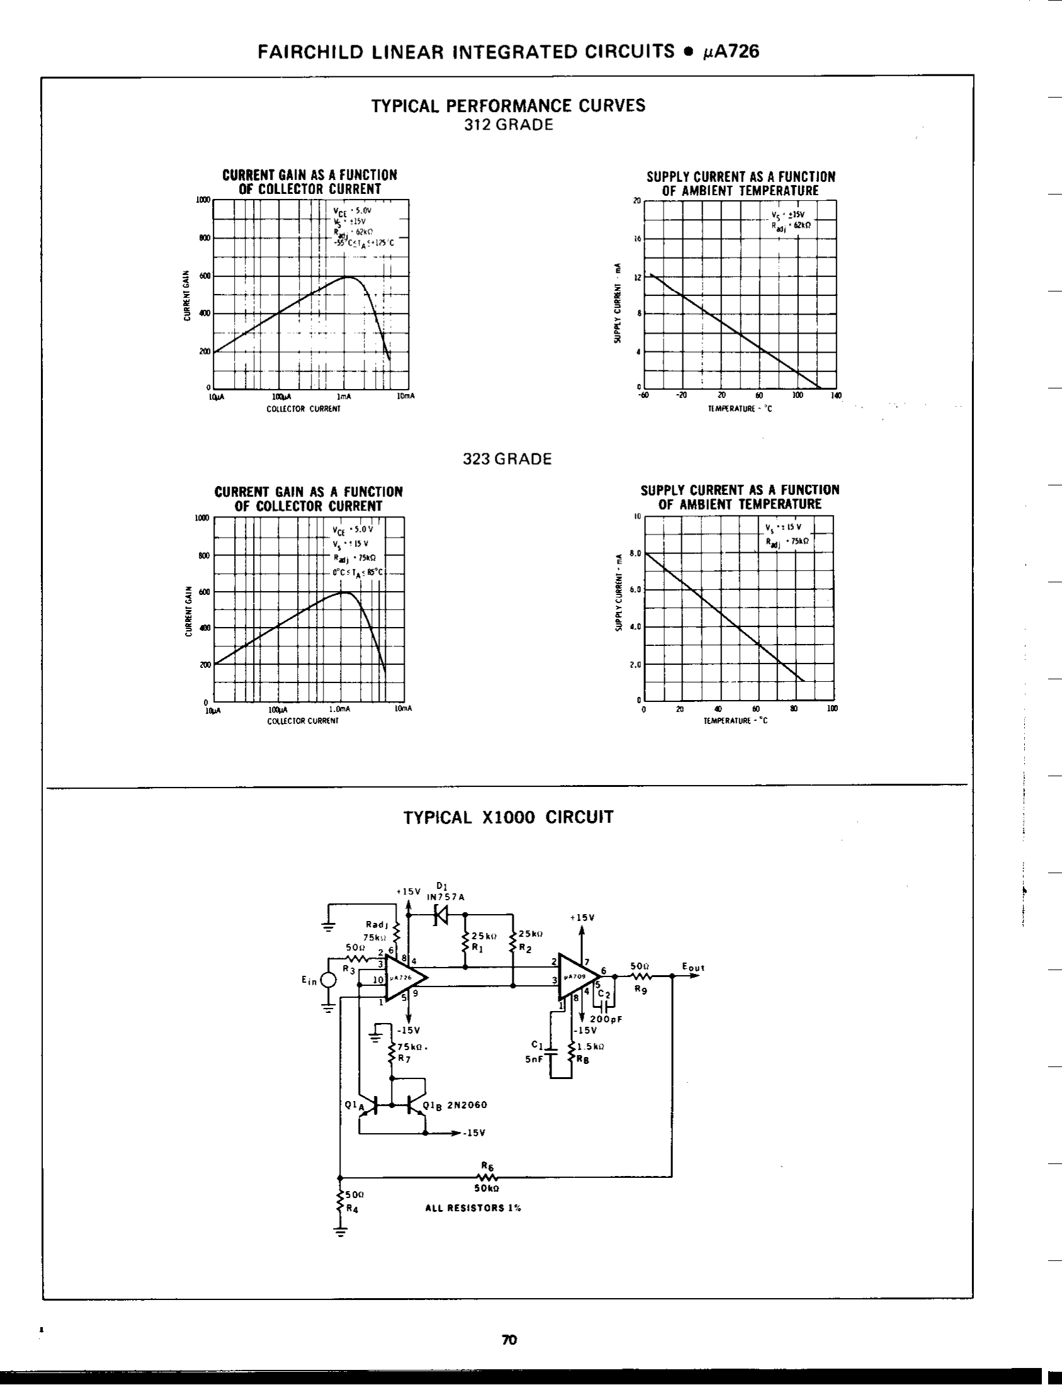
[picture p158: page 3]
