Baphomet2015/Formant_V2/Componentes_Electronicos/Notas/Conversores_DA/TL431.jpg

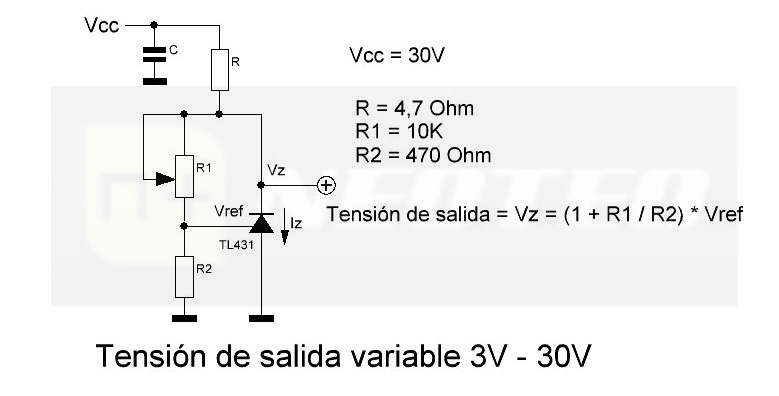
Componentes_Electronicos/Notas/Conversores_DA/TL431.jpg
