Baphomet2015/Formant_V2/Componentes_Electronicos/Notas/OP_Comparador/OP_Comparador.jpg

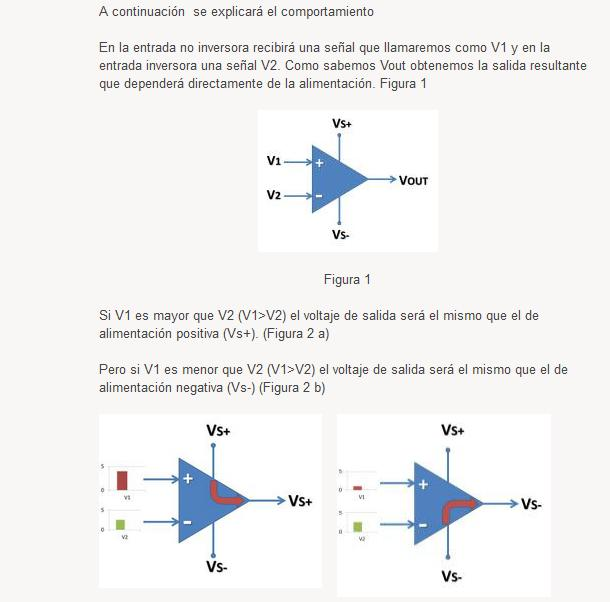
Componentes_Electronicos/Notas/OP_Comparador/OP_Comparador.jpg
