Baphomet2015/Formant_V2/Componentes_Mecanicos/Caratulas/ADSR/Caratula_ADSR.jpg

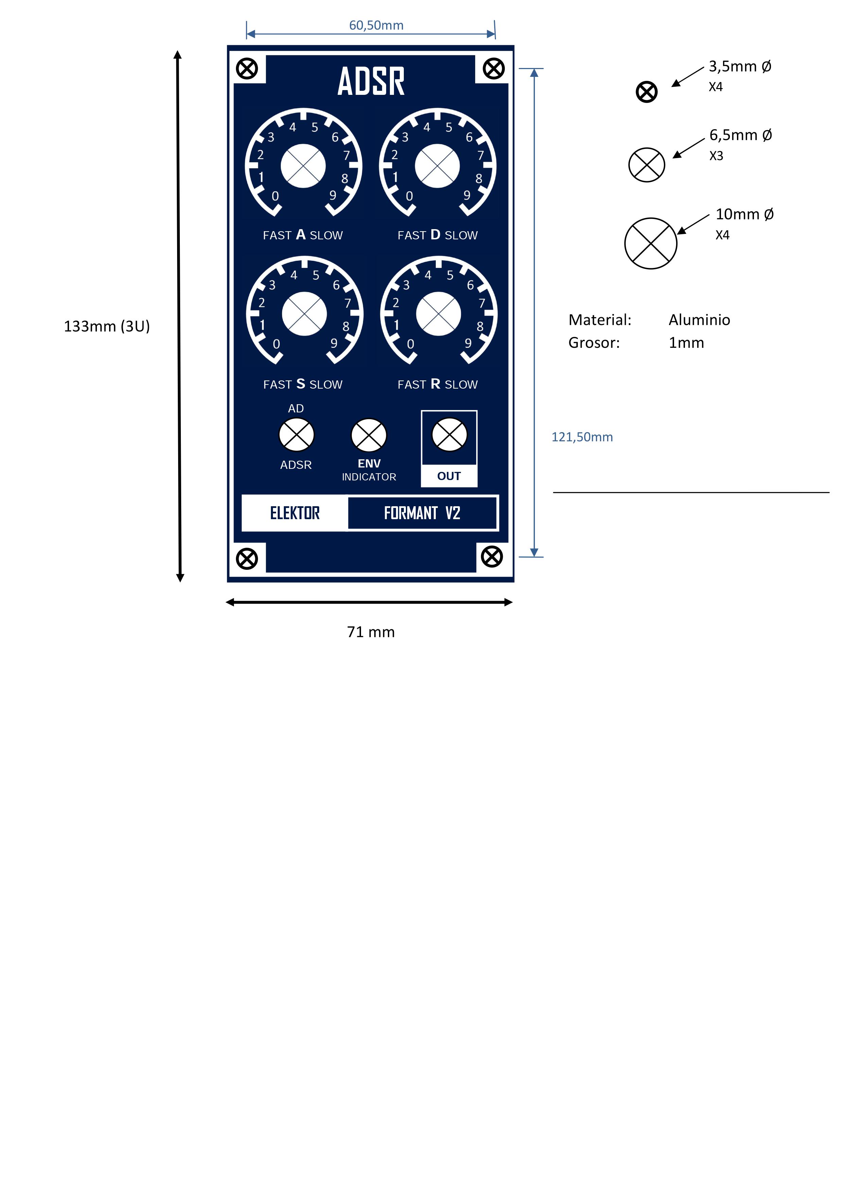
Componentes_Mecanicos/Caratulas/ADSR/Caratula_ADSR.jpg
