Baphomet2015/Formant_V2/Componentes_Mecanicos/Caratulas/INTERFACE-TECLADO/Caratula_INTERFACE.jpg

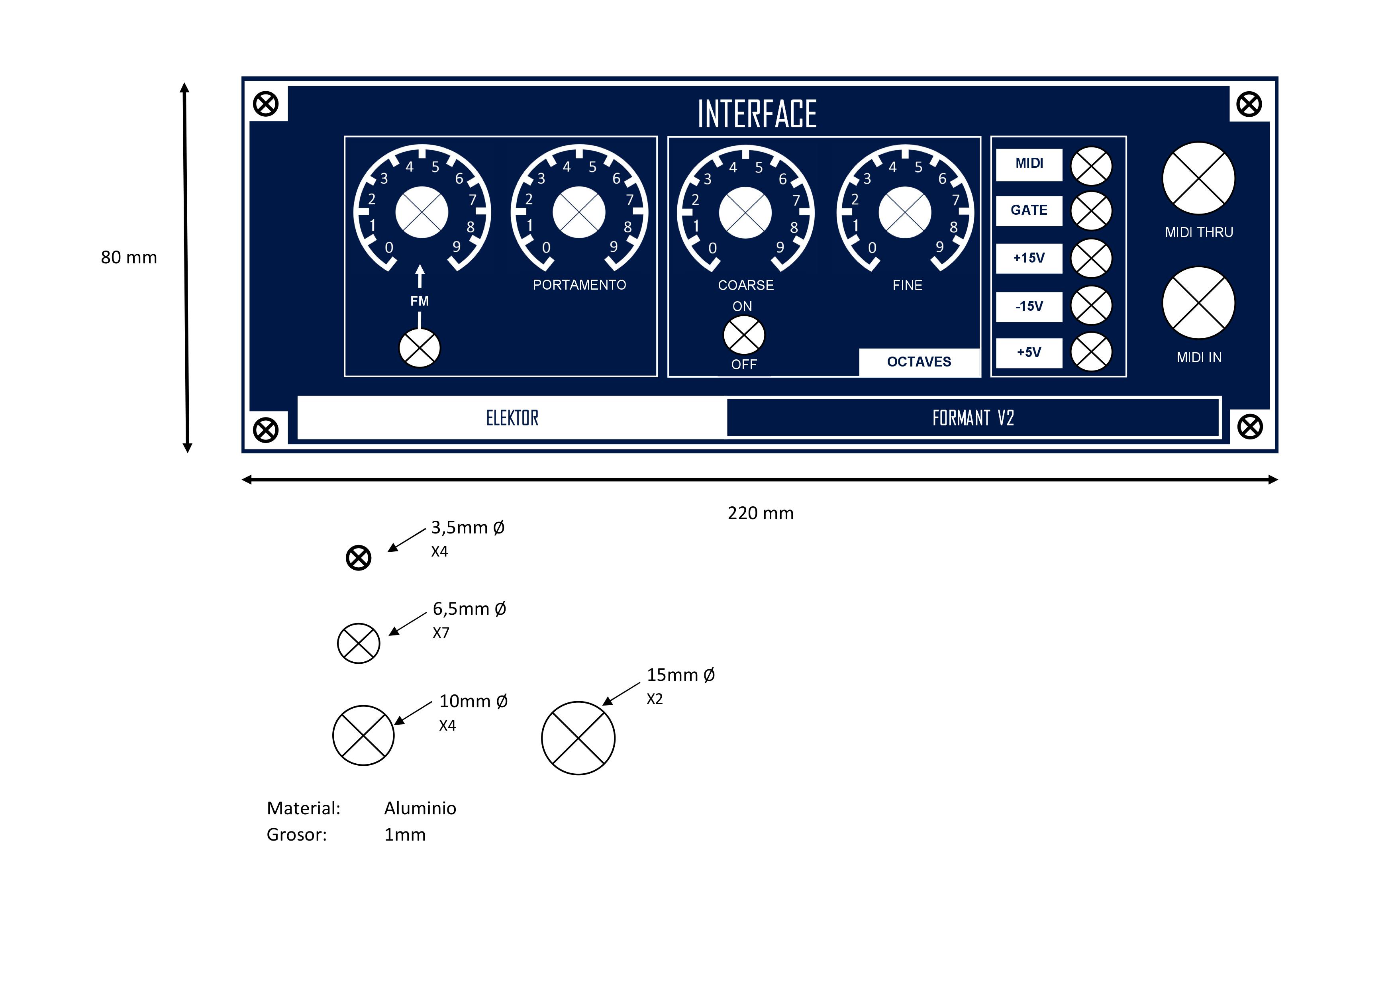
Componentes_Mecanicos/Caratulas/INTERFACE-TECLADO/Caratula_INTERFACE.jpg
