Baphomet2015/Formant_V2/Componentes_Mecanicos/Caratulas/Presupuestos_171004/Antonio Arnaiz-ref 001 (Caratula 71x266mm) 10-10-2017.jpg

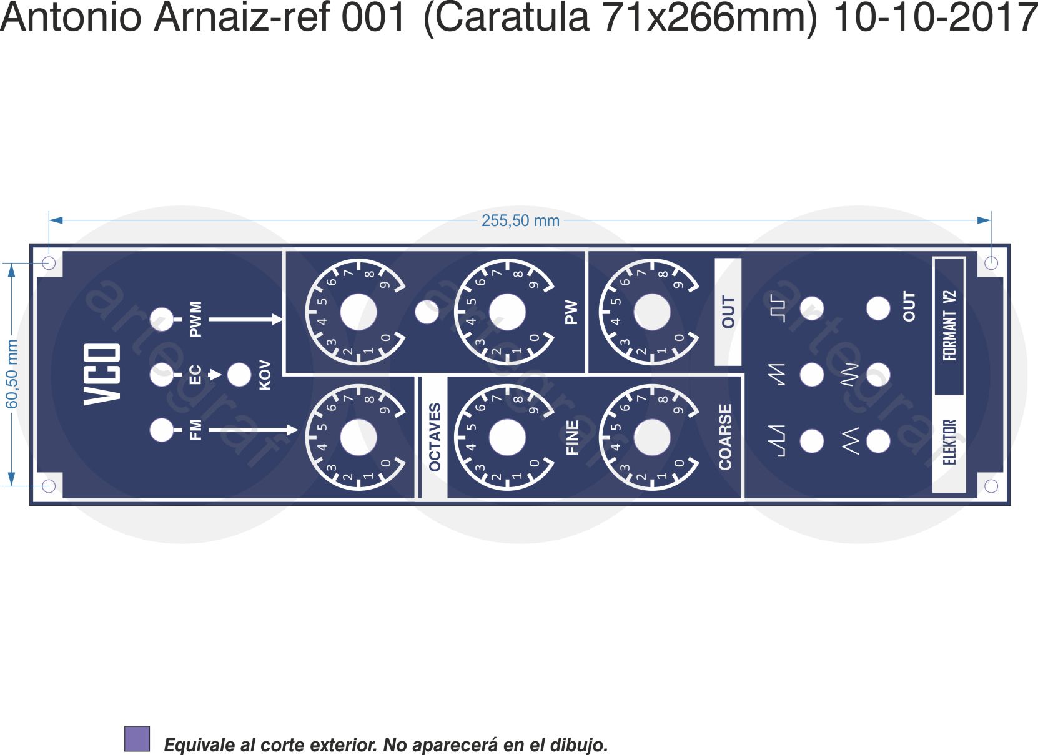
Componentes_Mecanicos/Caratulas/Presupuestos_171004/Antonio Arnaiz-ref 001 (Caratula 71x266mm) 10-10-2017.jpg
