Baphomet2015/Formant_V2/Componentes_Mecanicos/Caratulas/Presupuestos_171028/Antonio Arnaiz-ref 008 (Caratula 71x133mm) 22-11-2017.jpg

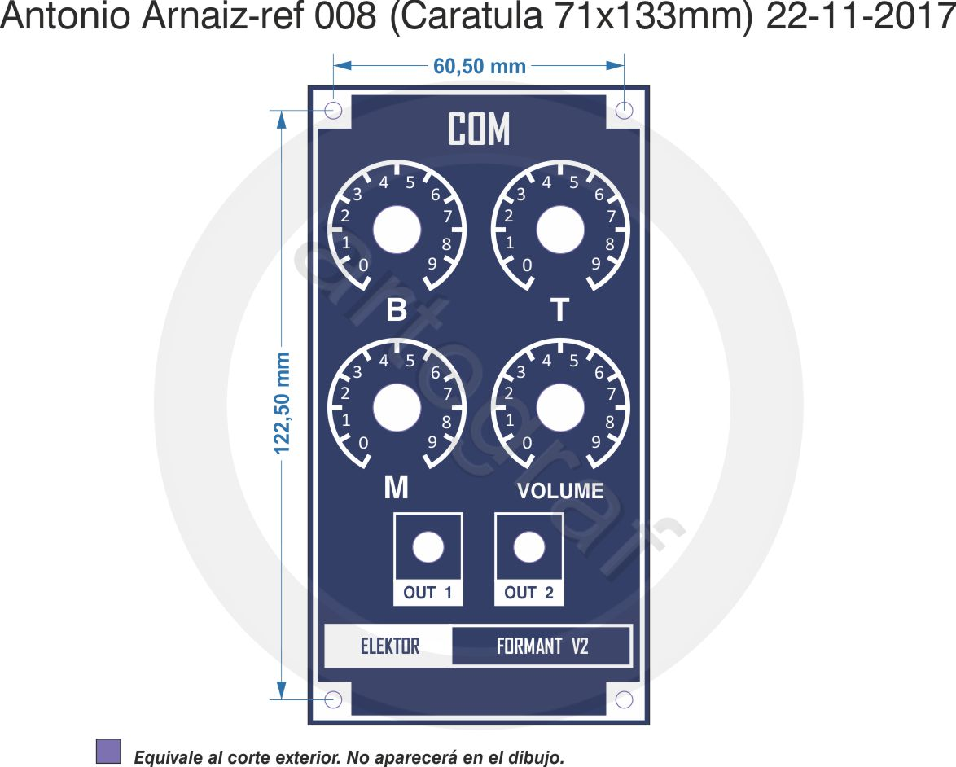
Componentes_Mecanicos/Caratulas/Presupuestos_171028/Antonio Arnaiz-ref 008 (Caratula 71x133mm) 22-11-2017.jpg
