Baphomet2015/Formant_V2/Componentes_Mecanicos/Caratulas/Varios/Caratula_Escala.jpg

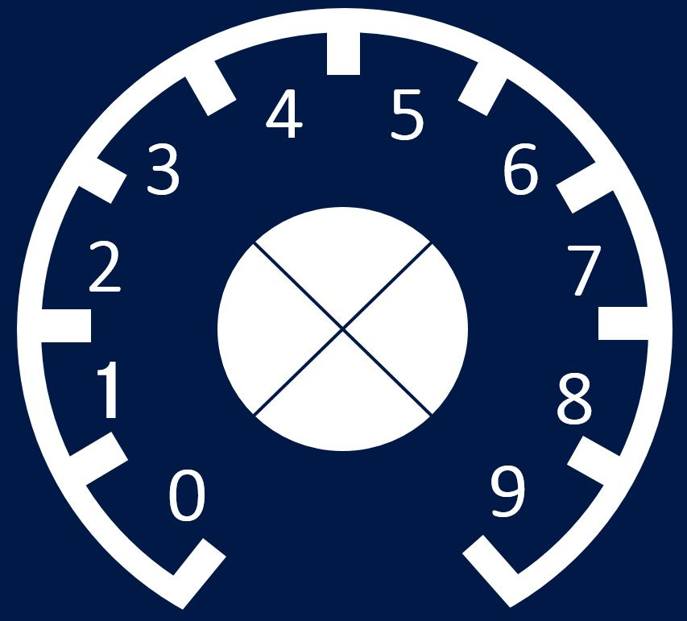
Componentes_Mecanicos/Caratulas/Varios/Caratula_Escala.jpg
