Baphomet2015/Formant_V2/Componentes_Mecanicos/Caratulas/Varios/Caratula_Escala_Comnutador.jpg

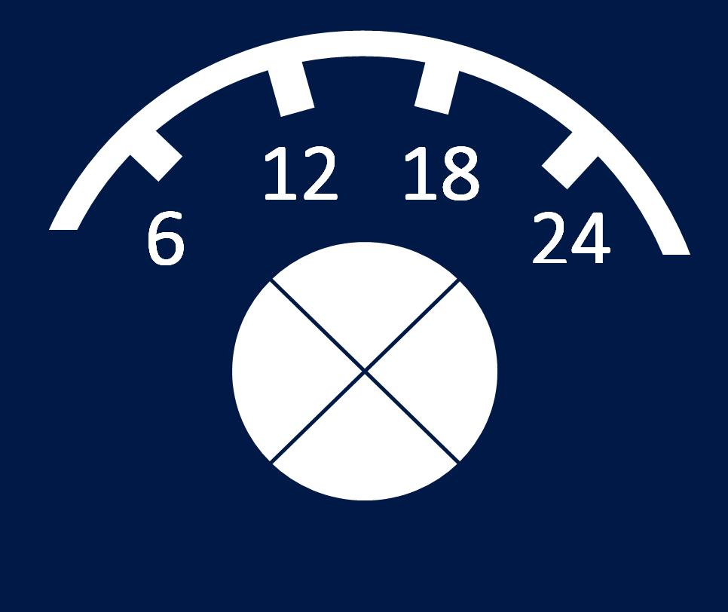
Componentes_Mecanicos/Caratulas/Varios/Caratula_Escala_Comnutador.jpg
