Baphomet2015/Formant_V2/Componentes_Mecanicos/Caratulas/VCF_12dB/Caratula_VCF_12dB.jpg

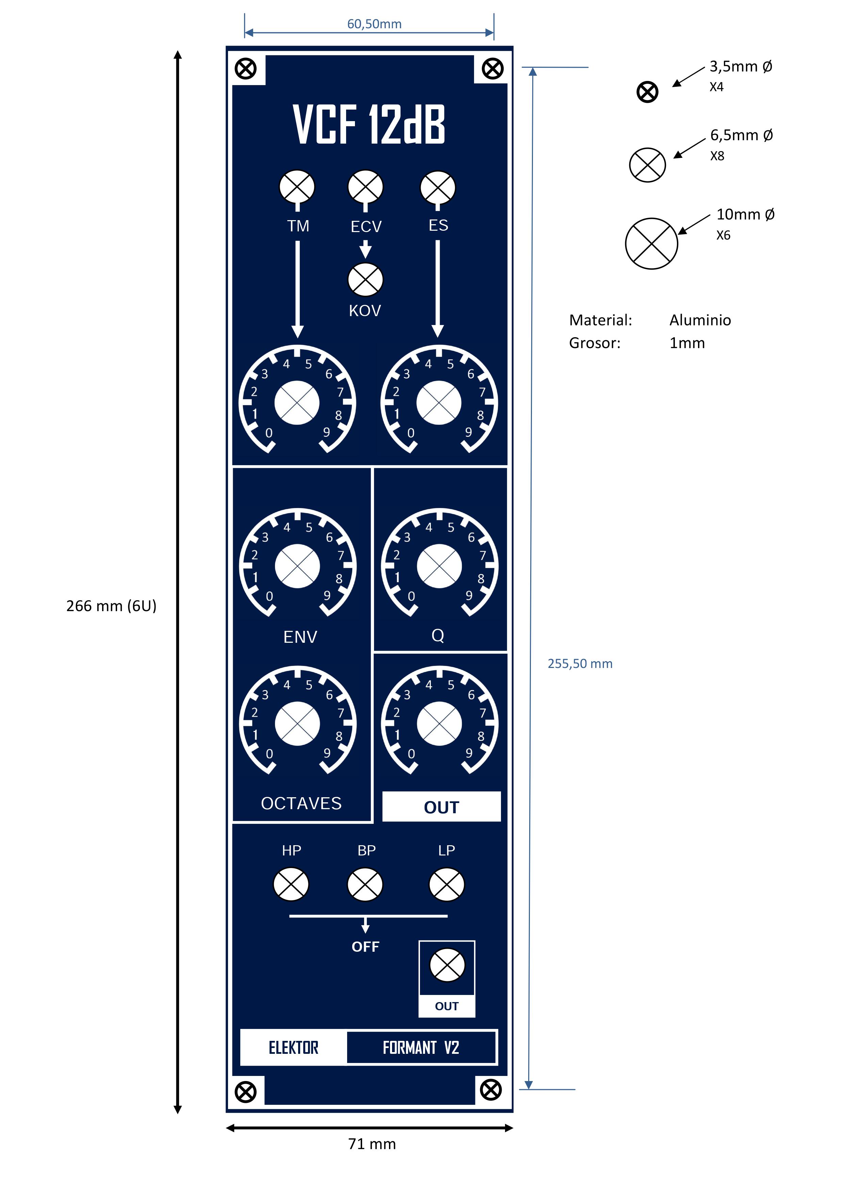
Componentes_Mecanicos/Caratulas/VCF_12dB/Caratula_VCF_12dB.jpg
