Baphomet2015/Formant_V2/Componentes_Mecanicos/Mueble_Racks/Fotos/P_20171125_213724.jpg

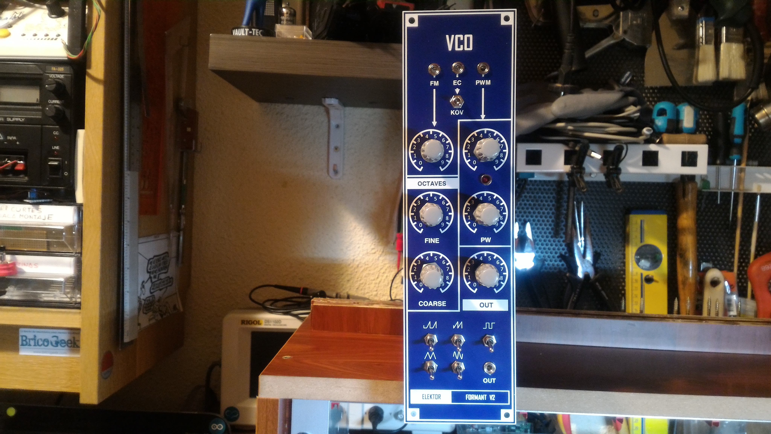
Componentes_Mecanicos/Mueble_Racks/Fotos/P_20171125_213724.jpg
