Baphomet2015/Formant_V2/Componentes_Mecanicos/Mueble_Racks/Fotos/P_20171202_134544.jpg

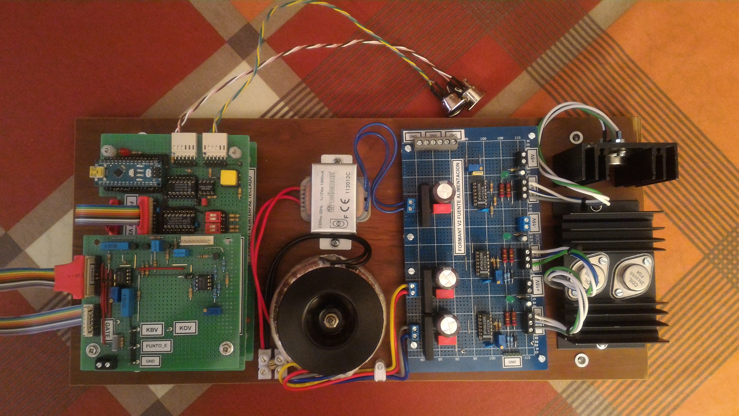
Componentes_Mecanicos/Mueble_Racks/Fotos/P_20171202_134544.jpg
