Baphomet2015/Formant_V2/Componentes_Mecanicos/Mueble_Racks/Fotos/P_20171206_110241.jpg

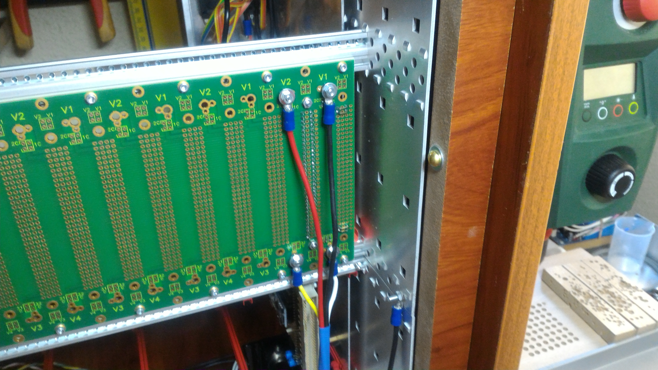
Componentes_Mecanicos/Mueble_Racks/Fotos/P_20171206_110241.jpg
