Baphomet2015/Formant_V2/Componentes_Mecanicos/Mueble_Racks/Tableros_Sanz.jpg

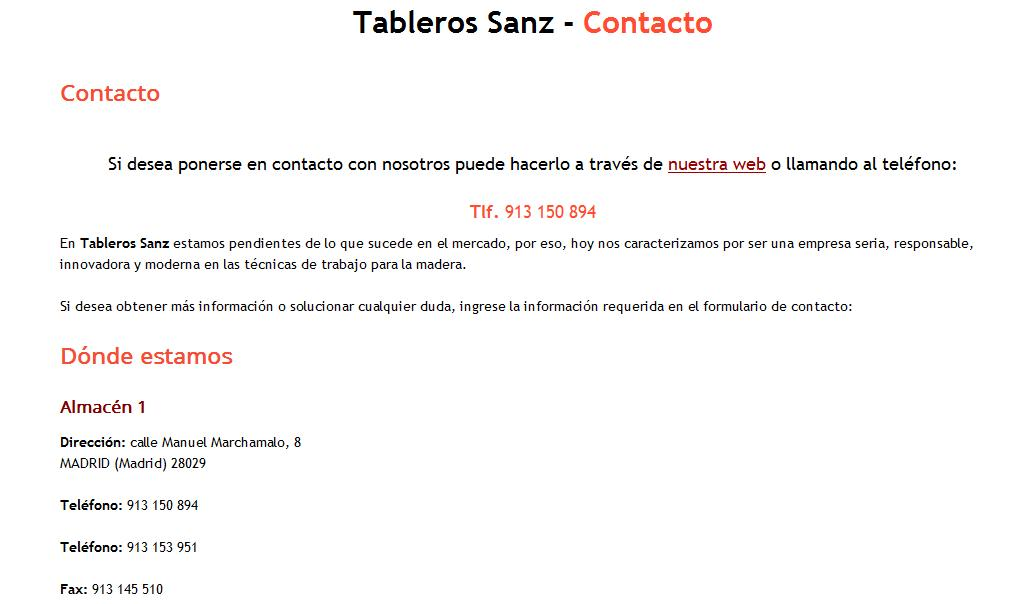
Componentes_Mecanicos/Mueble_Racks/Tableros_Sanz.jpg
