Baphomet2015/Formant_V2/Modulos/RITMOS/Roland TR-909_2/9090_wiring.pdf

## WIRING FOR DRUM VOICE POTENTIOMETERS

L

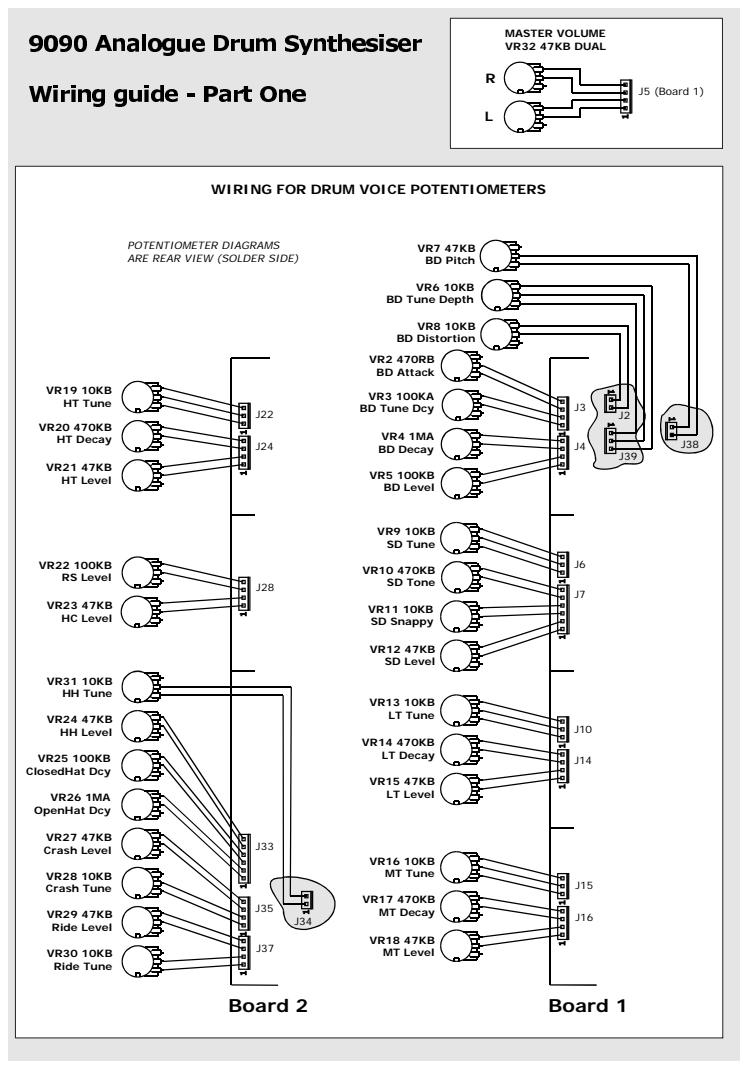
[picture p208: page 1]

POTENTIOMETER DIAGRAMS
ARE REAR VIEW (SOLDER SIDE)

1

## INDIVIDUAL VOICE OUTPUTS

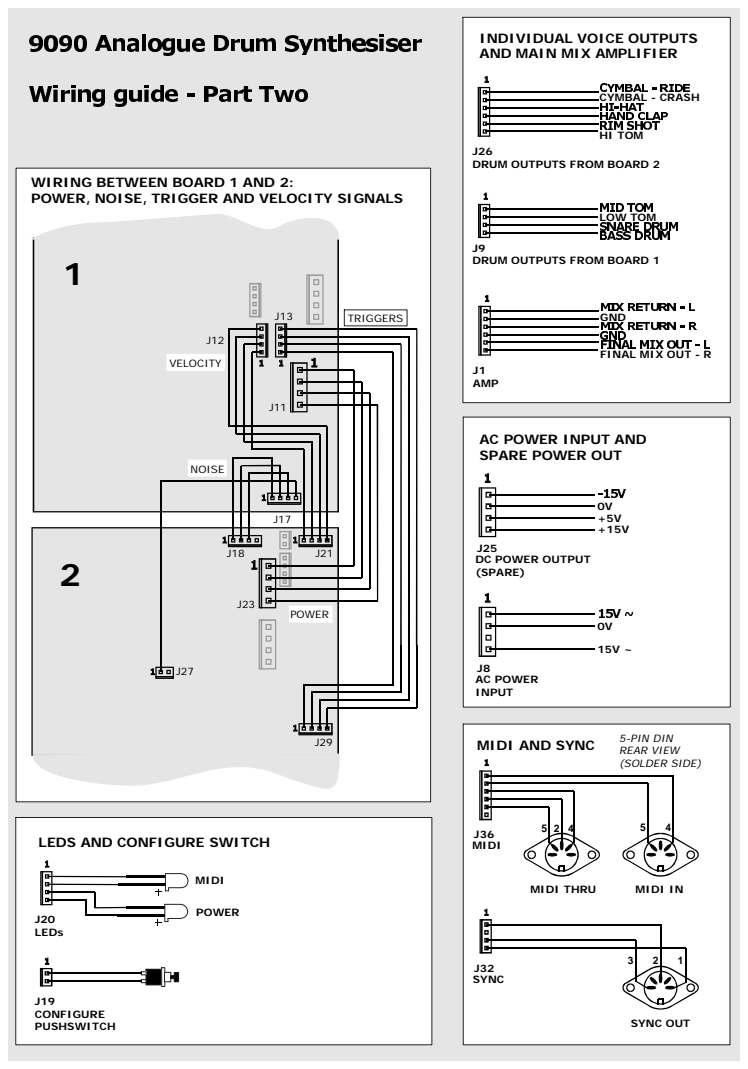
[picture p209: page 2]

AND MAIN MIX AMPLIFIER

WIRING BETWEEN BOARD1 AND 2:
POWER, NOISE, TRIGGER AND VELOCITY SIGNALS

AC POWER INPUT AND
SPARE POWER OUT

LEDS AND CONFIGURE SWITCH
