Baphomet2015/Formant_V2/Componentes_Mecanicos/Caratulas/LFOS/Caratula_LFO.pdf

# LFOs

1

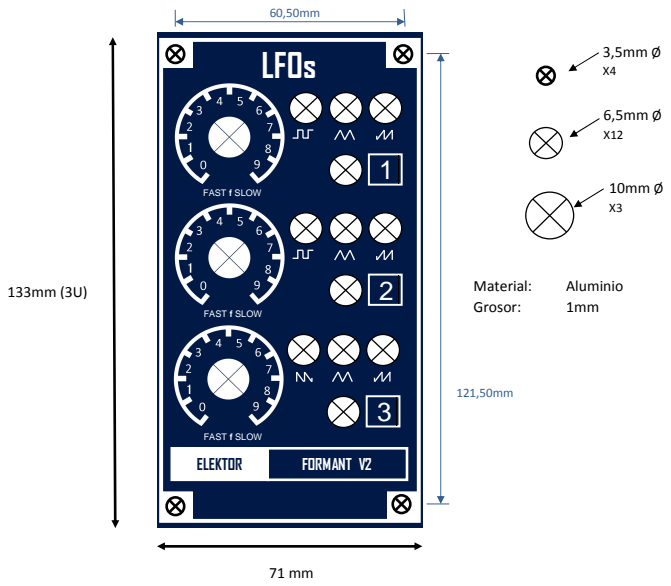
[picture p210: page 1]
Material:; Aluminio; Grosor:; ELEKTOR; FORMANT V2; FAST f SLOW
