Baphomet2015/Formant_V2/Componentes_Mecanicos/Caratulas/INTERFACE-TECLADO/Caratula_INTERFACE.pdf

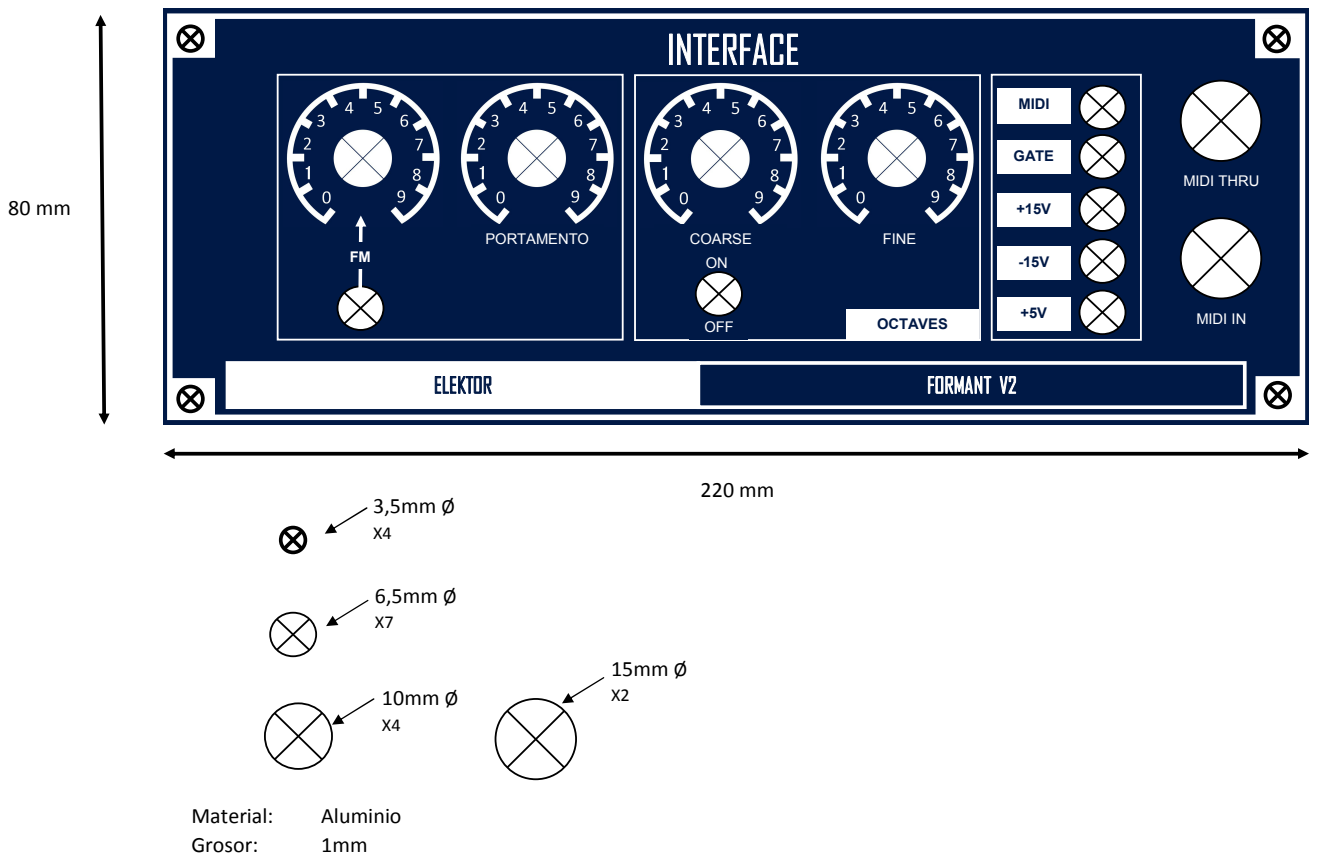
[picture p211: page 1]
INTERFACE ELEKTOR; FORMANT V2 GATE MIDI +15V -15V +5V; Material:; Aluminio; Grosor:; PORTAMENTO; COARSE; FINE; OFF; OCTAVES; MIDI IN; MIDI THRU
