Baphomet2015/Formant_V2/Componentes_Mecanicos/Caratulas/VCF_12dB/Caratula_VCF_12dB.pdf

# VCF 12dB

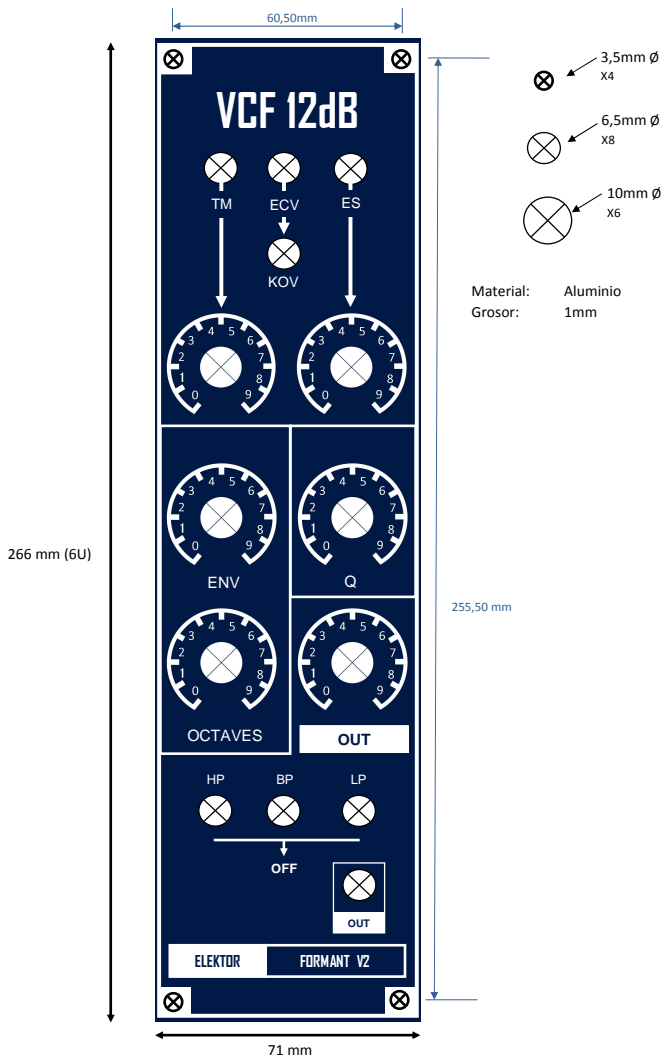
[picture p212: page 1]
ELEKTOR; FORMANT V2; ENV; OCTAVES; OUT; Material:; Aluminio; Grosor:; OFF; KOV; ECV
