Baphomet2015/Formant_V2/Componentes_Mecanicos/Caratulas/DUAL_VCA/Caratula_VCA.pdf

# DUAL VCA

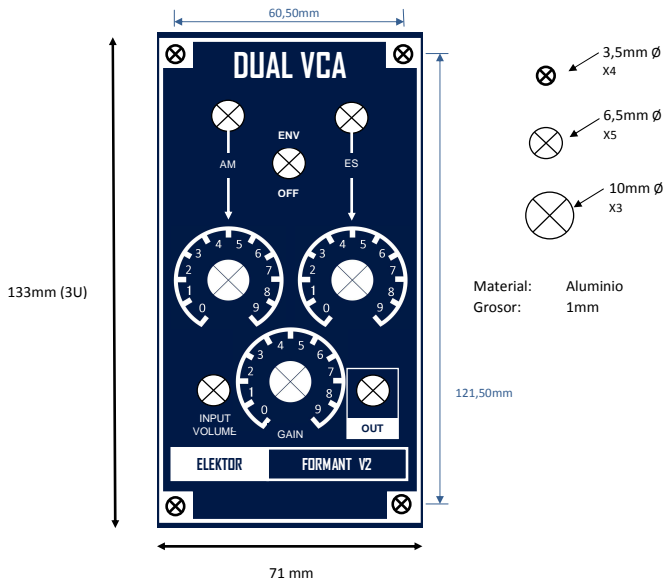
[picture p213: page 1]
Material:; Aluminio; Grosor:; GAIN; ELEKTOR; FORMANT V2; INPUT VOLUME; OFF; ENV; OUT
