Baphomet2015/Formant_V2/Componentes_Mecanicos/Caratulas/VCF_24dB/Caratula_VCF_24dB.pdf

# VCF 24dB

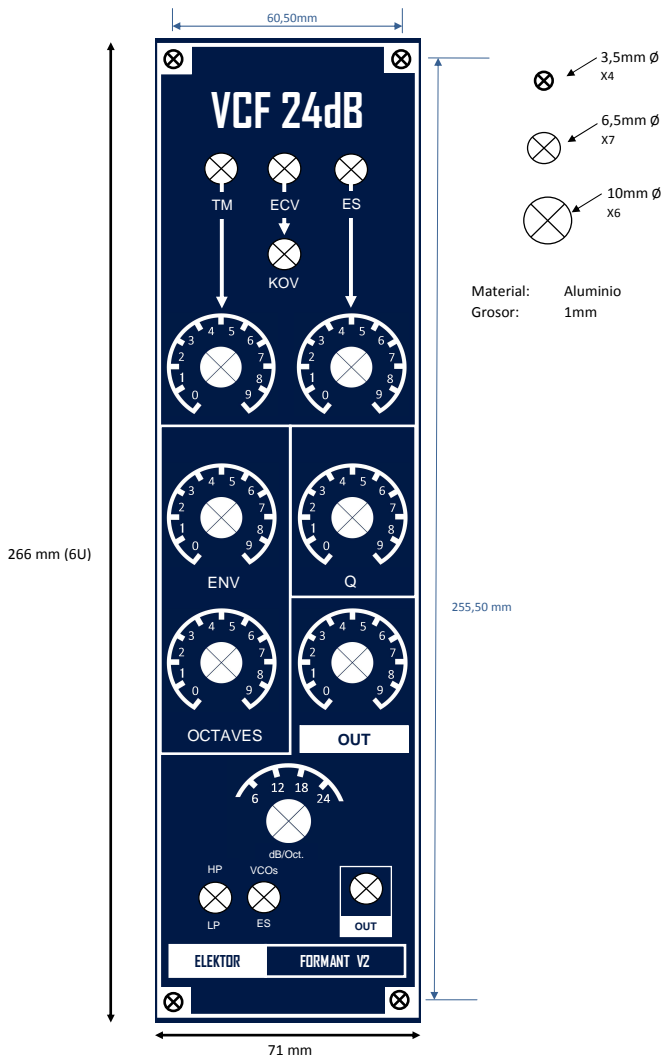
[picture p214: page 1]
ELEKTOR; FORMANT V2; ENV; OCTAVES; OUT; Material:; Aluminio; Grosor:; KOV; ECV; VCOs; dB/Oct.
