Baphomet2015/Formant_V2/Componentes_Mecanicos/Caratulas/VCO/Caratula_VCO.pdf

# VCO

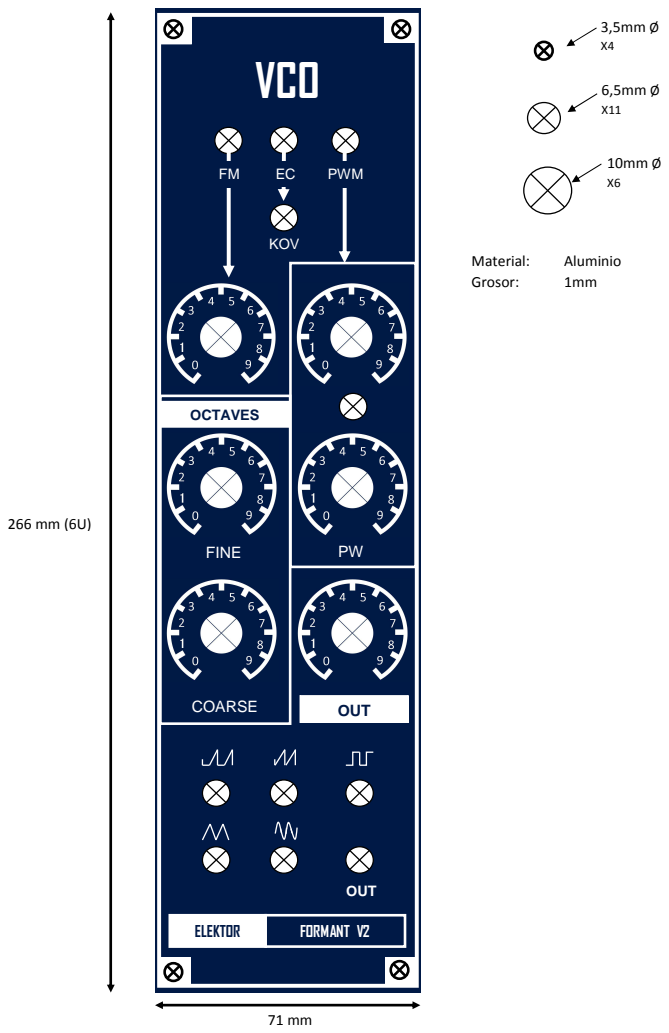
[picture p215: page 1]
ELEKTOR; FORMANT V2; OCTAVES; FINE; COARSE; OUT; Material:; Aluminio; Grosor:; KOV; PWM
