Baphomet2015/Formant_V2/Componentes_Mecanicos/Mueble_Racks/Bastidor de Rack aal Detalle de incrustación de tuerca.pdf

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

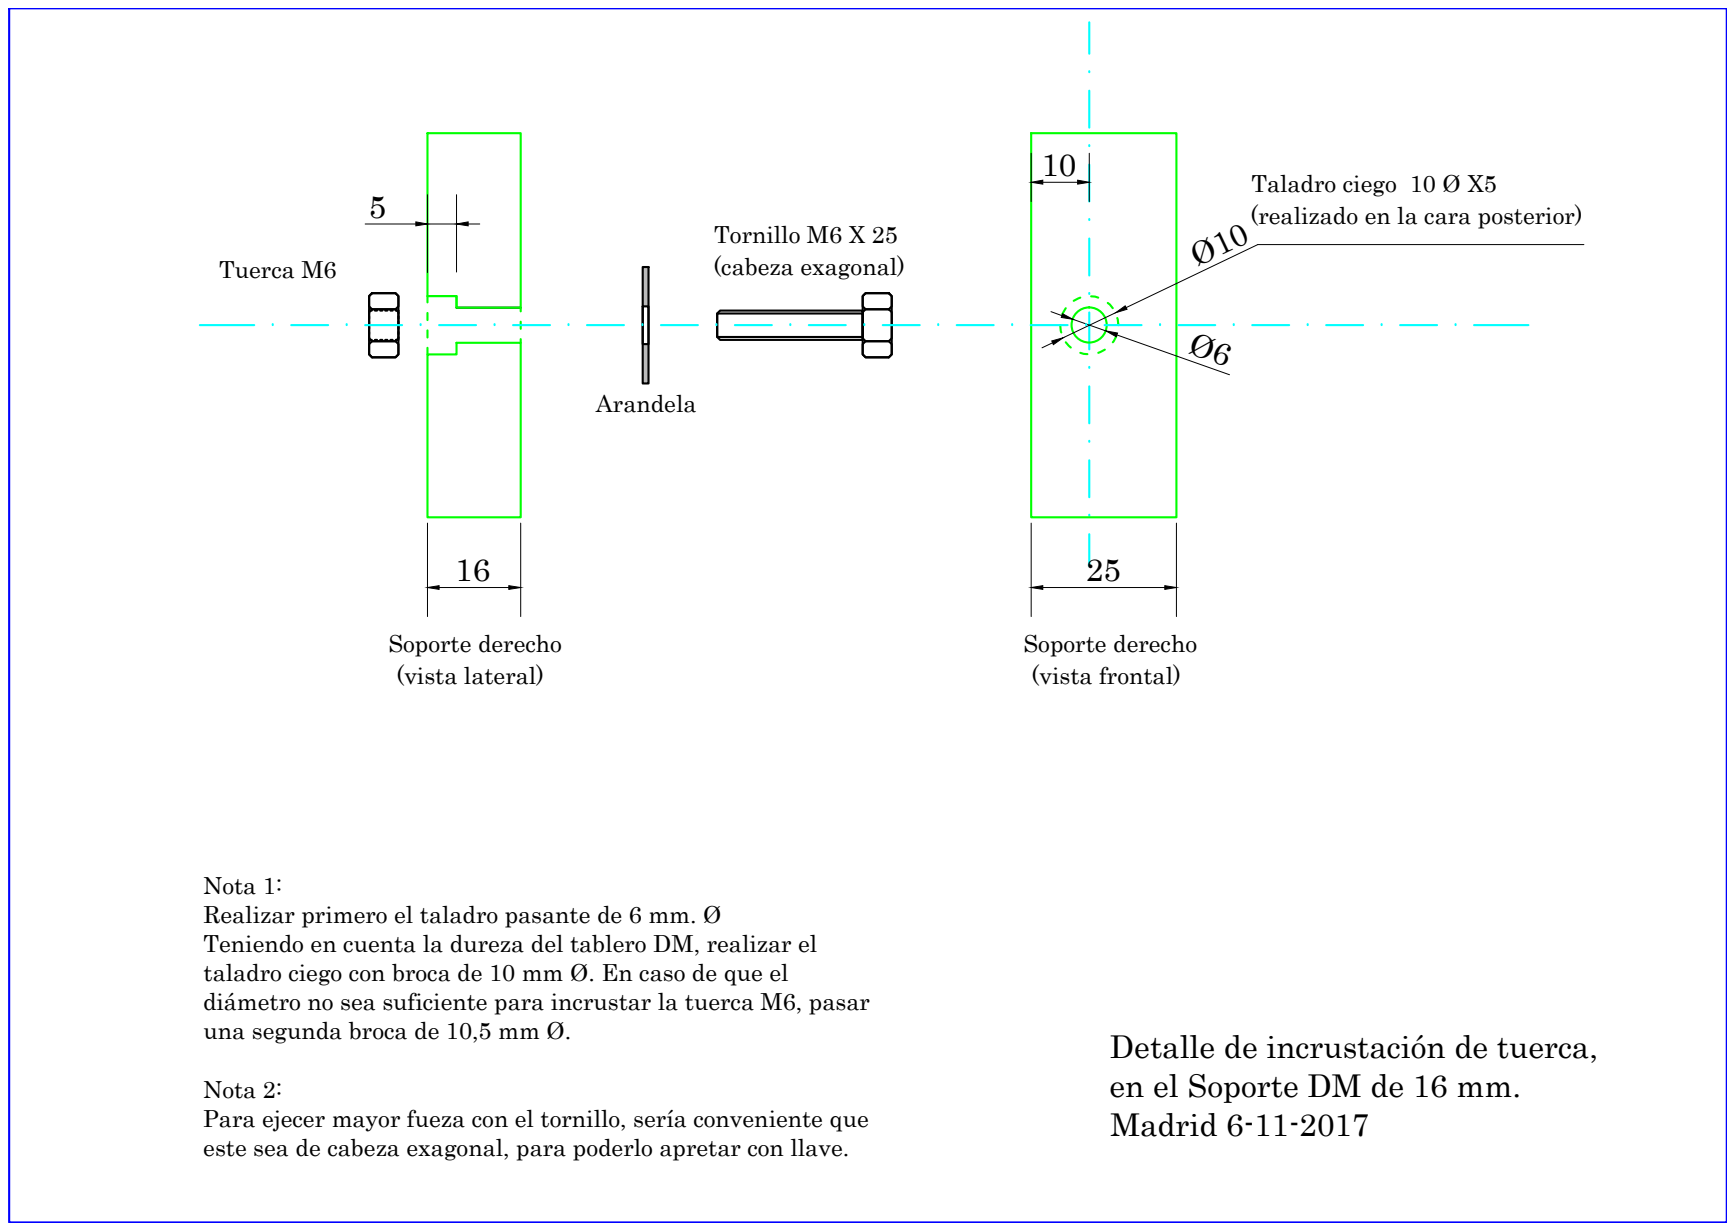
[picture p216: page 1]
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
