Baphomet2015/Formant_V2/Componentes_Mecanicos/Mueble_Racks/Bastidor de Rack aal Detalle Soporte con tuerca M6.pdf

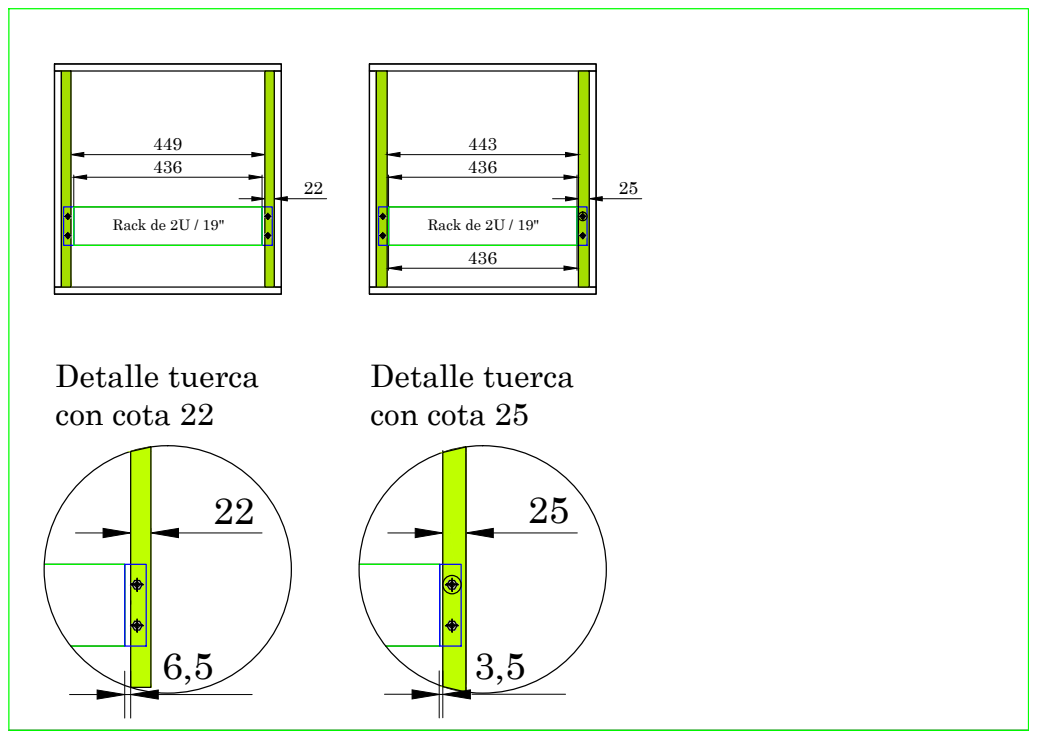
[picture p217: page 1]
22 449 Rack de 2U / 19"; 25 Rack de 2U / 19" 443 436; 436 22 6,5 Detalle tuerca con cota 22; Detalle tuerca con cota 25
