Baphomet2015/Formant_V2/Modulos/ADSR/Hw/Formant_V2_ADSR.kicad_pcb

## KiCad design diagrams/schematic/Firefly.sch

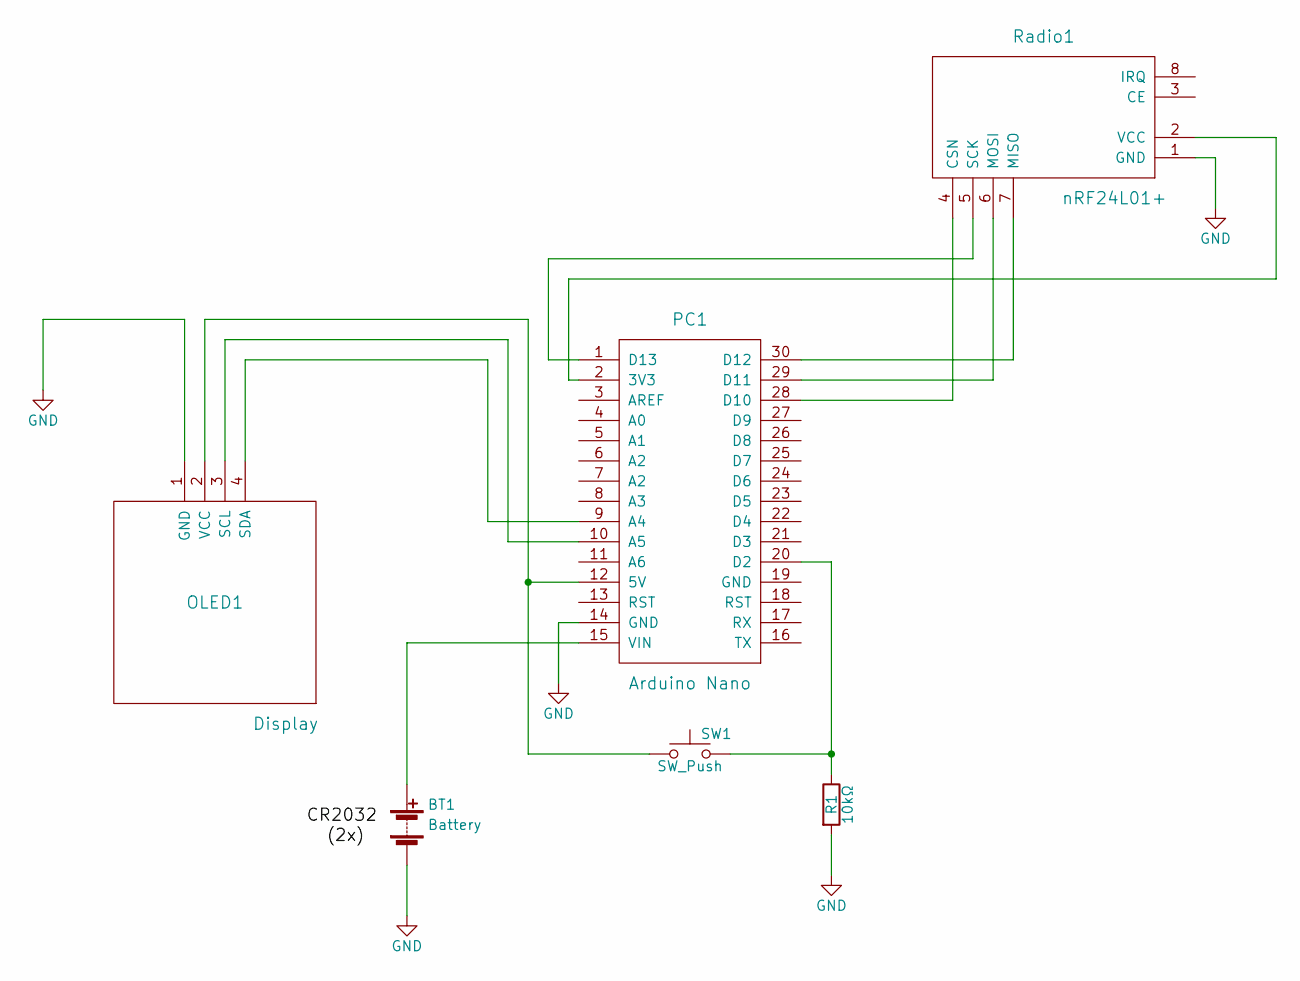
[picture p218: schematic Firefly.sch]

Parts:
10kΩ: R1
BT1: Battery
OLED1: Display
PC1: Arduino Nano
Radio1: nRF24L01+
SW1: SW_Push

Connections:
GND: 10kΩ.2, BT1.2 (-), OLED1.1 (GND), PC1.14 (GND), Radio1.1 (GND)
unnamed: 10kΩ.1, PC1.20 (D2), SW1.2
unnamed: BT1.1 (+), PC1.15 (VIN)
unnamed: OLED1.2 (VCC), PC1.12 (5V), SW1.1
unnamed: OLED1.3 (SCL), PC1.10 (A5)
unnamed: OLED1.4 (SDA), PC1.9 (A4)
unnamed: PC1.1 (D13), Radio1.5 (SCK)
unnamed: PC1.2 (3V3), Radio1.2 (VCC)
unnamed: PC1.28 (D10), Radio1.4 (CSN)
unnamed: PC1.29 (D11), Radio1.6 (MOSI)
unnamed: PC1.30 (D12), Radio1.7 (MISO)
