Baphomet2015/Formant_V2/Modulos/VCO/Hw/Formant_V2_VCO_CEM3340.sch

## KiCad design Modulos/VCO/Hw/Formant_V2_VCO_CEM3340.sch (2019-10-20)

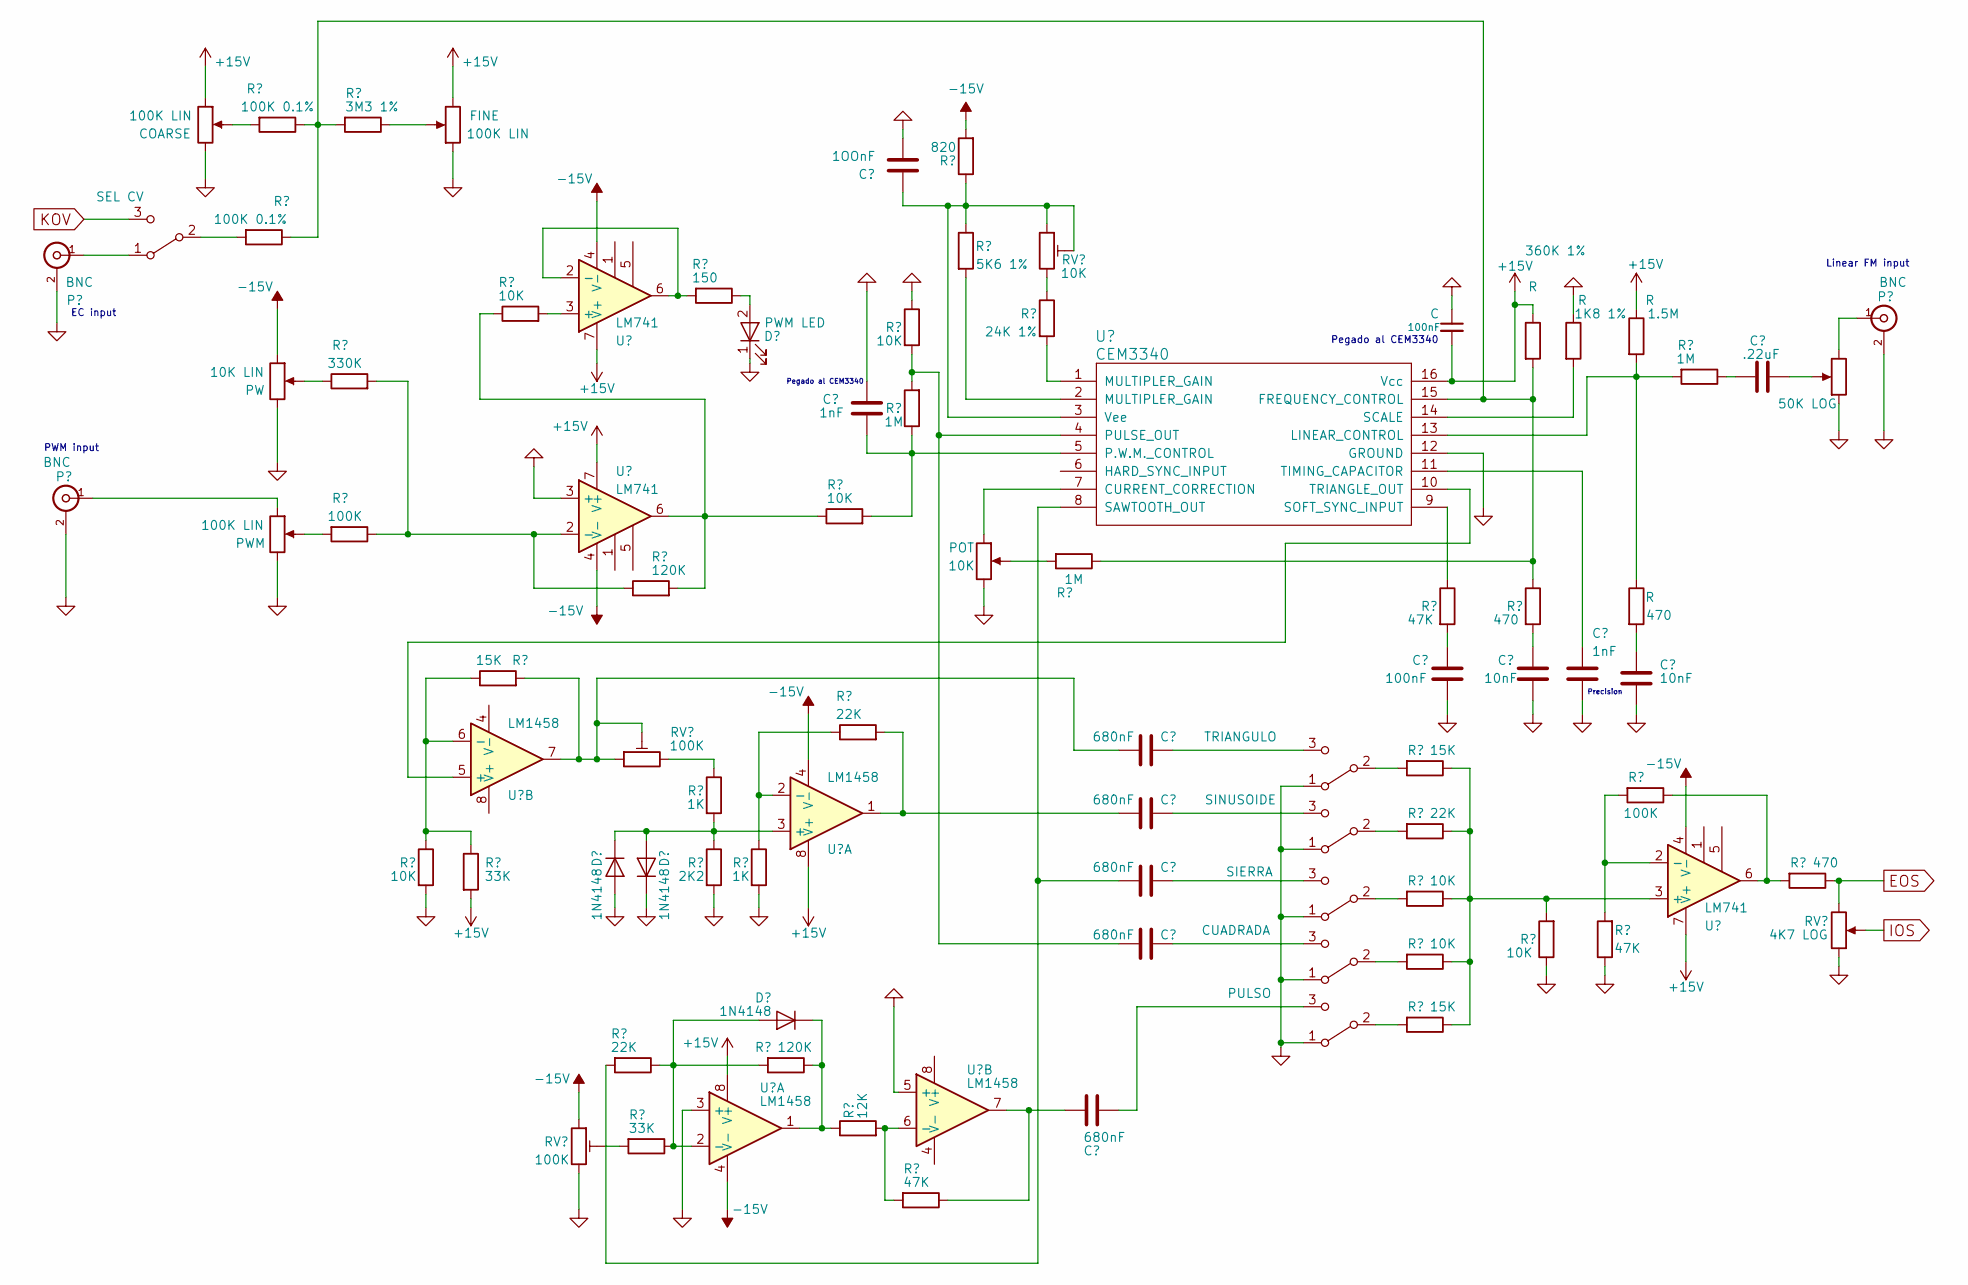
[picture p219: schematic Formant_V2_VCO_CEM3340.sch]

Parts:
10K: POT
C: 100nF
COARSE: 100K LIN
FINE: 100K LIN
PW: 10K LIN
PWM: 100K LIN
R: 360K 1%

Connections:
+15V: C.2, COARSE.1, FINE.3, R.1
-15V: PW.1
GND: 10K.3, C.1, COARSE.3, FINE.1, PW.3, PWM.3, R.1
unnamed: R.1, R.2

Notes on the sheet:
Linear FM input
Pegado al CEM3340
Precision
PWM input
EC input
