Baphomet2015/Formant_V2/Modulos/INTERFACE-TECLADO/Hw/Ver_DAC_12Bits/Formant_V2_Teclado.sch

## KiCad design Modulos/INTERFACE-TECLADO/Hw/Ver_DAC_12Bits/Formant_V2_Teclado.sch (2019-10-06)

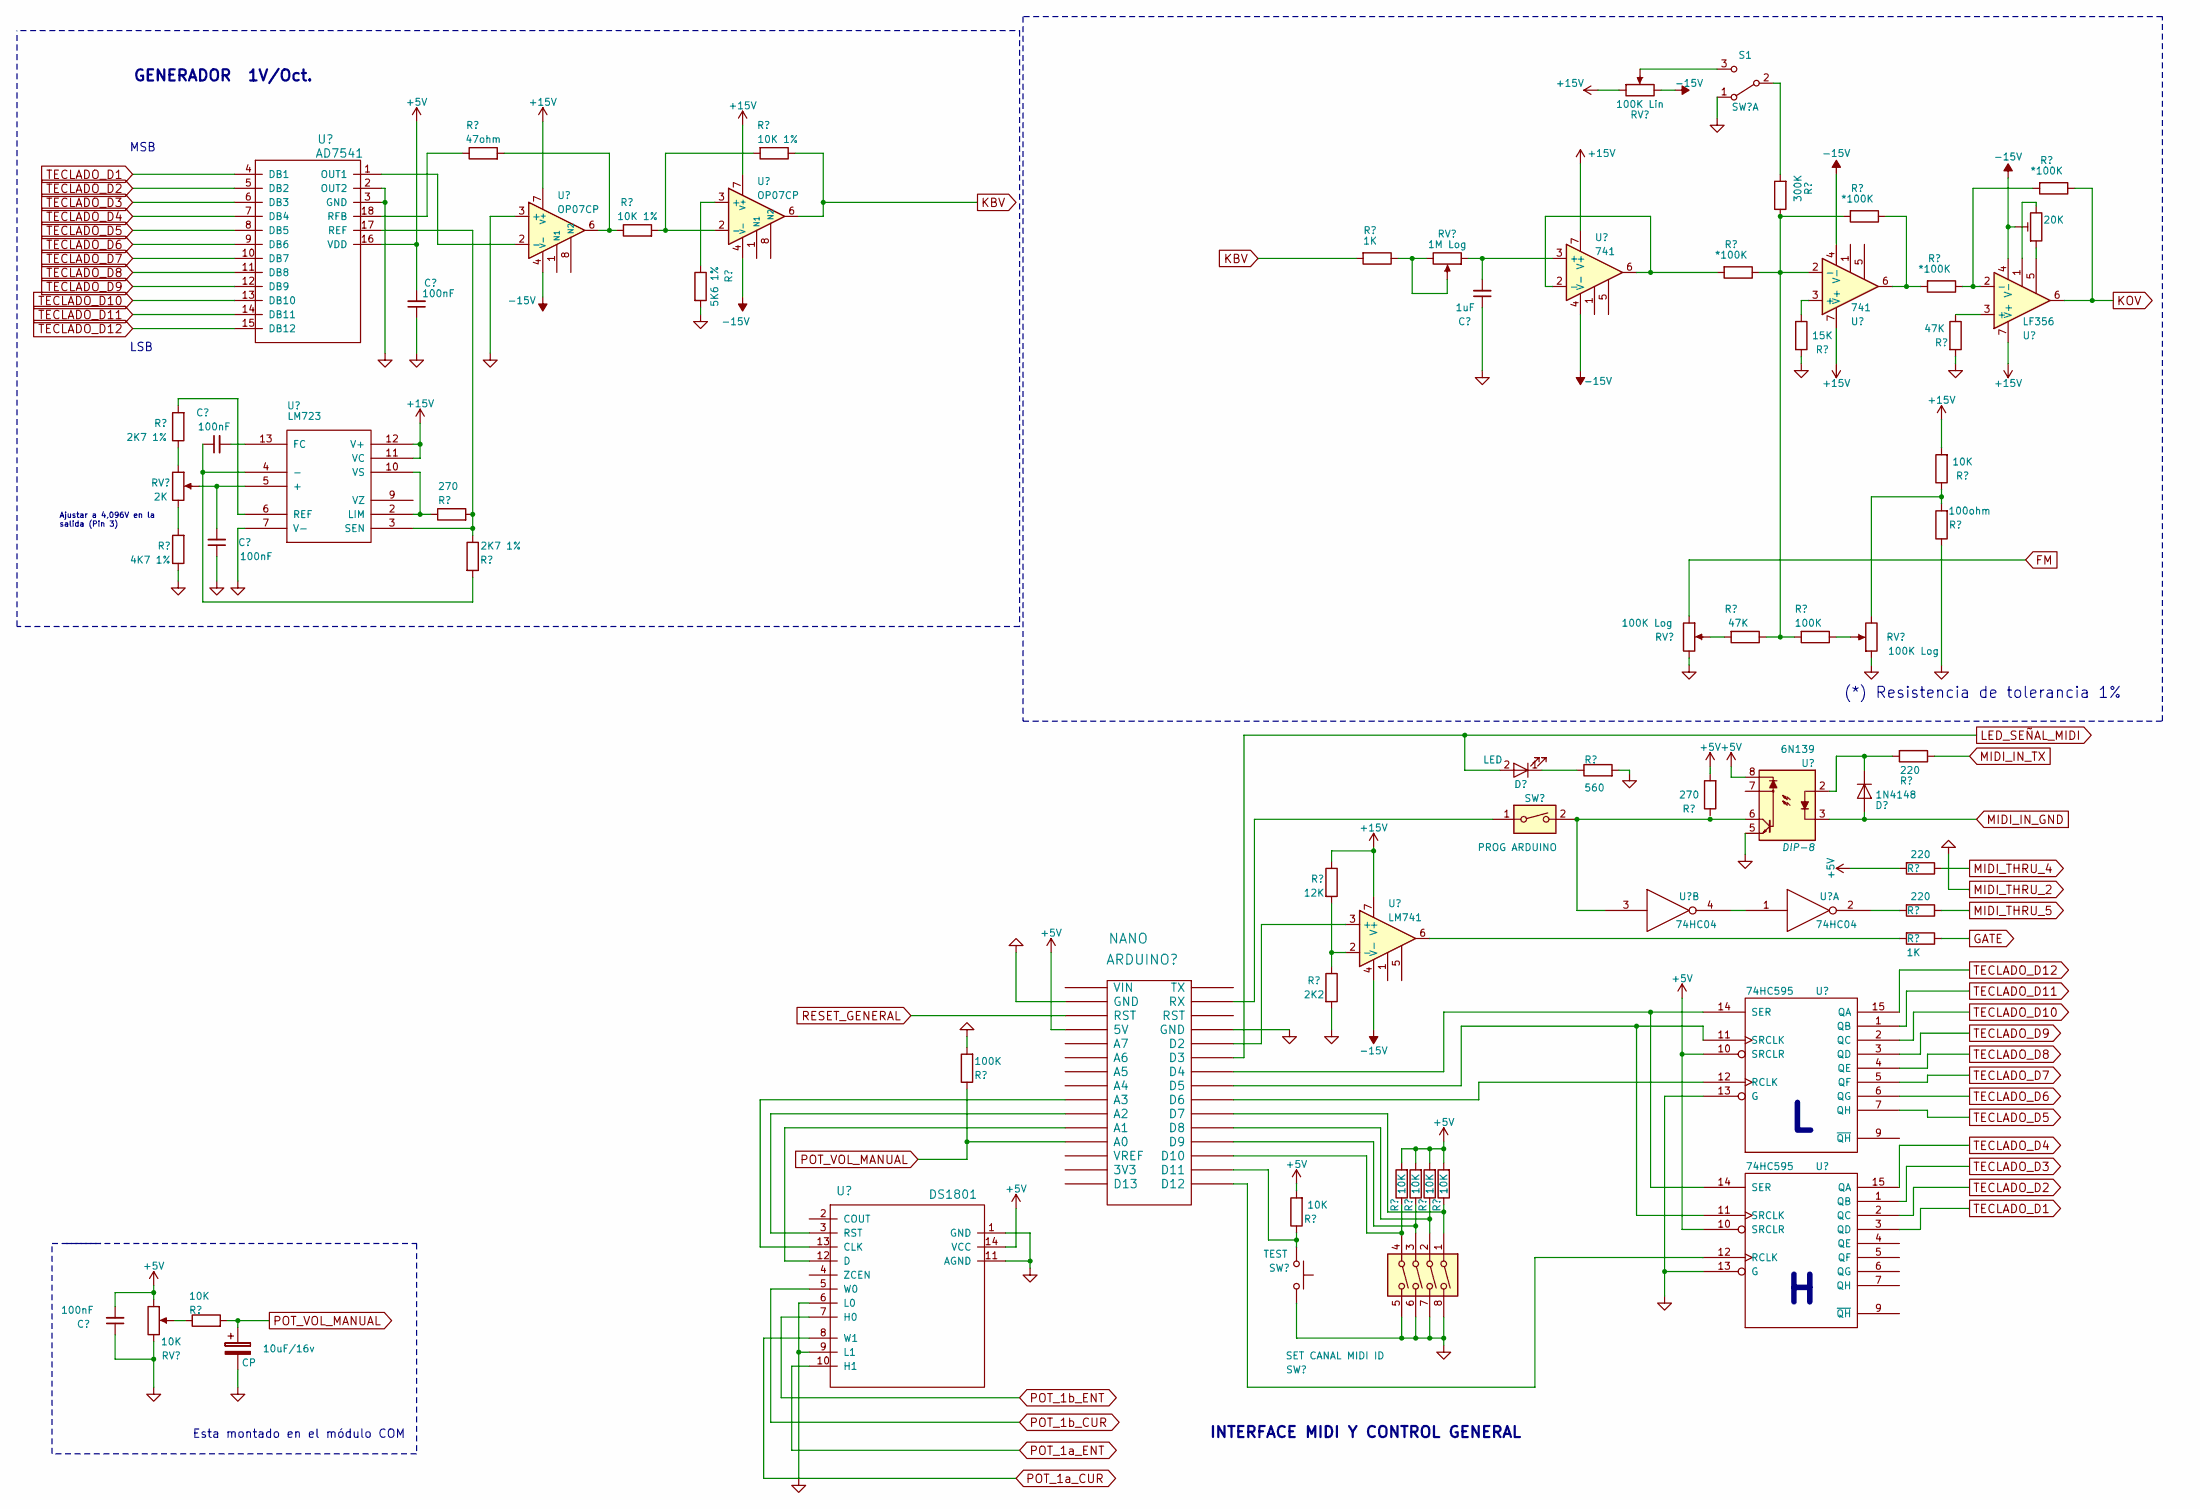
[picture p220: schematic Formant_V2_Teclado.sch]

Parts:
10uF/16v: CP
20K: POT_TRIM

Connections:
-15V: 20K.2
GND: 10uF/16v.2
POT_VOL_MANUAL: 10uF/16v.1

Notes on the sheet:
Esta montado en el módulo COM
LSB
MSB
GENERADOR 1V/Oct.
INTERFACE MIDI Y CONTROL GENERAL
Ajustar a 4,096V en la salida (Pin 3)
(*) Resistencia de tolerancia 1%
