Baphomet2015/Formant_V2/Modulos/ADSR/Sw/Formant_V2_ADSR/Formant_V2_ADSR.ino

// ---------------------------------------------------------
//
// Proyecto:       Formant_V2
// Version:        1.0
// Fichero:        Formant_V2_ADSR.ino
// Autor:   
// Hardware:       Arduino Nano V3.0
// Fecha:          Noviembre 2017
//
// Funcionalidad:  Fichero principal ( main ) de la aplicacion
//                 de control del generador de ADSR.
//
// Notas:          REVISADO --        
//
// ---------------------------------------------------------

#include <Arduino.h>
#include <stdlib.h>
#include "ADSR.h"
#include "Formant_V2_ADSR.h"





// ------------------------------------------------------------
//
//
//
//
// ------------------------------------------------------------

ARDUINO_ADSR adsr_1;
ARDUINO_ADSR adsr_2;

byte flg_GATE;



// ------------------------------------------------------------
//
// setup()
//
//
// ------------------------------------------------------------

void setup()
{
   pinMode(IDE_HW_PIN_GATE,INPUT);

   Serial.begin(9600);
   
   adsr_1.begin( IDE_HW_PIN_ADSR_1_A   ,
                 IDE_HW_PIN_ADSR_1_D   , 
                 IDE_HW_PIN_ADSR_1_S   ,
                 IDE_HW_PIN_ADSR_1_R   , 
                 IDE_HW_PIN_ADSR_1_OUT ,
                 IDE_HW_PIN_ADSR_1_MODO
                );

   adsr_2.begin( IDE_HW_PIN_ADSR_2_A    ,
                 IDE_HW_PIN_ADSR_2_D    ,
                 IDE_HW_PIN_ADSR_2_S    ,
                 IDE_HW_PIN_ADSR_2_R    ,  
                 IDE_HW_PIN_ADSR_2_OUT  ,
                 IDE_HW_PIN_ADSR_2_MODO
                );
   
}





// ------------------------------------------------------------
//
// void loop()
//
// ------------------------------------------------------------

void loop()
{

  // ------------------------------------------------------------
  // .
  // .
  // .
  // ------------------------------------------------------------
  getGATE();
  
  // ------------------------------------------------------------
  // .
  // .
  // .
  // ------------------------------------------------------------
  adsr_1.generar(flg_GATE);
  adsr_2.generar(flg_GATE);

}




// ------------------------------------------------------------
//
// Lee la senal de GATE y actualiza el flag global
//
// ------------------------------------------------------------

void getGATE(void)
{
  if ( digitalRead(IDE_HW_PIN_GATE)==HIGH )
     { // ------------------------------------------------------------
       // Senal GATE activa
       // ------------------------------------------------------------
       #ifdef DEBUG_ADSR
       if ( flg_GATE!=IDE_GATE_ON ) { Serial.println("ON"); }
       #endif
       flg_GATE = IDE_GATE_ON;
     }
  else
     { // ------------------------------------------------------------
       // Senal GATE inactiva
       // ------------------------------------------------------------
       #ifdef DEBUG_ADSR
       if ( flg_GATE!=IDE_GATE_OFF ) { Serial.println("OFF"); }
       #endif
       flg_GATE = IDE_GATE_OFF;
     }
  
}
