Baphomet2015/Formant_V2/Modulos/ADSR/Sw/Formant_V2_ADSR/Formant_V2_ADSR.h

// ---------------------------------------------------------
//
// Proyecto:       Formant_V2
// Version:        1.0
// Fichero:        Formant_V2_ADSR.h
// Autor:   
// Hardware:       Arduino Nano V3.0
// Fecha:          Noviembre 2017
//
// Funcionalidad:  Fichero principal ( main ) de la aplicaciÃ³n
//                 de control del generador de ADSR.
//
// Notas:          REVISADO --        
//
// ---------------------------------------------------------

#ifndef FORMANT_V2_ADSR
#define FORMANT_V2_ADSR


// ---------------------------------------------------------
//                        ATENCION:
// DESCOMENTAR este define para compilar trazas de depuracion
// que se envian por el pueerto serie
// ---------------------------------------------------------

//#define DEBUG_ADSR  1


// ---------------------------------------------------------
//
// Defines de la aplicacion
//
// ---------------------------------------------------------

#define IDE_HW_PIN_GATE          12   // Pin para recibir la seÃ±al de disparo (GATE)

#define IDE_HW_PIN_ADSR_1_A       2   // Pin para generar la parte ATTACK  en el ADSR 1 DIGITAL
#define IDE_HW_PIN_ADSR_1_D       3   // Pin para generar la parte DECAY   en el ADSR 1 DIGITAL
#define IDE_HW_PIN_ADSR_1_R       4   // Pin para generar la parte RELEASE en el ADSR 1 DIGITAL
#define IDE_HW_PIN_ADSR_1_OUT    A0   // Pin para leer la tension de salida del ADSR
#define IDE_HW_PIN_ADSR_1_S      A1   // Pin para generar la parte SUSTAIN en el ADSR 1 
#define IDE_HW_PIN_ADSR_1_MODO   11   // Para seleccionar el modo AD/ADSR en el ASDSR 1


#define IDE_HW_PIN_ADSR_2_A       5   // Pin para generar la parte ATTACK  en el ADS 1 DIGITAL
#define IDE_HW_PIN_ADSR_2_D       6   // Pin para generar la parte DECAY   en el ADSR 1 DIGITAL
#define IDE_HW_PIN_ADSR_2_R       7   // Pin para generar la parte RELEASE en el ADSR 1 DIGITAL
#define IDE_HW_PIN_ADSR_2_OUT    A2   // Pin para leer la tension de salida del ADSR
#define IDE_HW_PIN_ADSR_2_S      A3   // Pin para generar la parte SUSTAIN en el ADSR 1 ANALOG
#define IDE_HW_PIN_ADSR_2_MODO   10   // Para seleccionar el modo AD/ADSR en el ASDSR 2


#define IDE_GATE_ON               1    // Senal GATE activa, se esta pulsando una tecla
#define IDE_GATE_OFF              0    // Senal GATE inactiva, NO se esta pulsando una tecla









#endif
